redstoner-35/DFEx-FloodBeaMon3tr/PCB/4S六层GaN驱动/生产资料/驱动正面高清图片.JPG

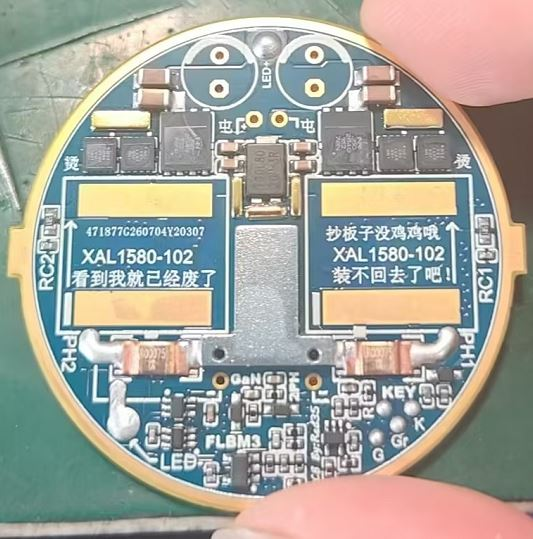
PCB/4S六层GaN驱动/生产资料/驱动正面高清图片.JPG
