redstoner-35/DFEx-FloodBeaMon3tr/PCB/4串主动均衡和BMS/生产资料/变压器样品照片.JPG

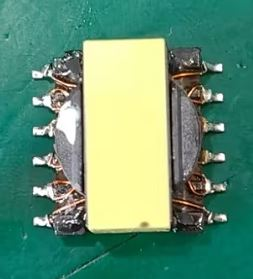
PCB/4串主动均衡和BMS/生产资料/变压器样品照片.JPG
