redstoner-35/DFEx-FloodBeaMon3tr/机械/光学相关文件/光杯尺寸图.jpg

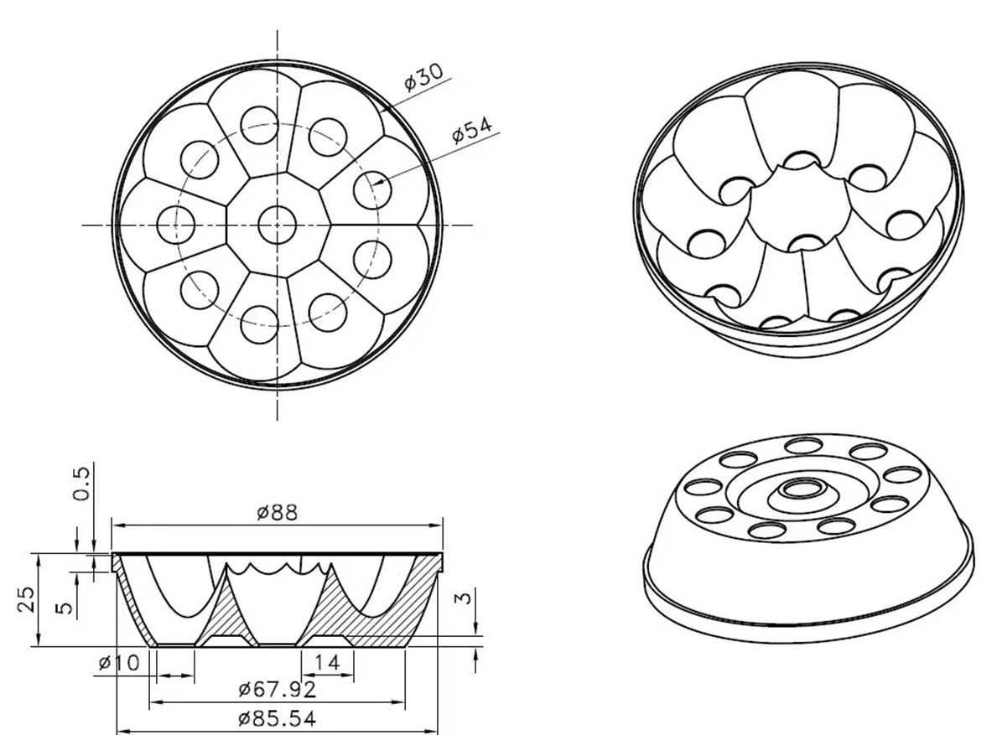
机械/光学相关文件/光杯尺寸图.jpg
