redstoner-35/DFEx-FloodBeaMon3tr/机械/光学相关文件/定位片样式.jpg

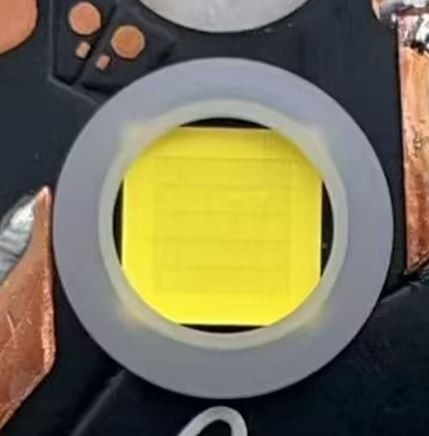
机械/光学相关文件/定位片样式.jpg
