redstoner-35/DFEx-FloodBeaMon3tr/机械/风扇把手相关3D制造文件/风扇手柄固定块.SLDPRT

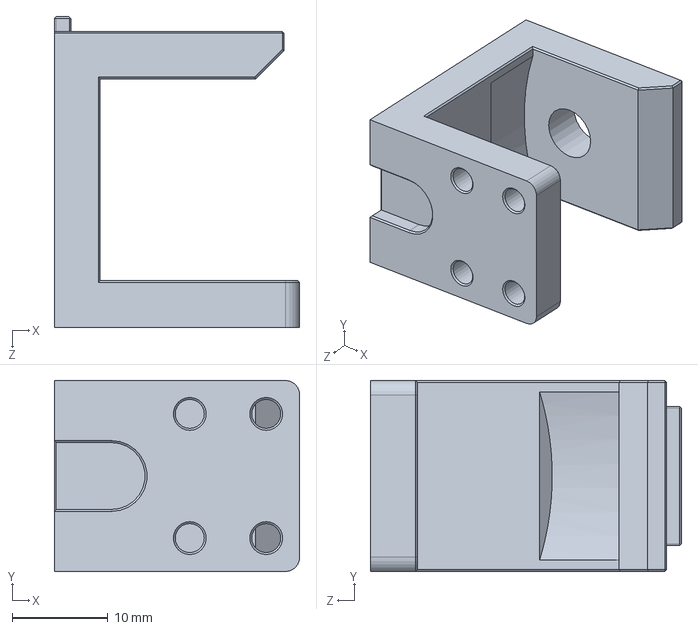
[picture p44: CAD file, 2026-08-25]
机械/风扇把手相关3D制造文件/风扇手柄固定块.SLDPRT
25.7 x 20.0 x 32.5 mm
