redstoner-35/DFEx-FloodBeaMon3tr/机械/驱动相关3D制造文件/驱动电流传导块-紫铜镀雾锡.STEP

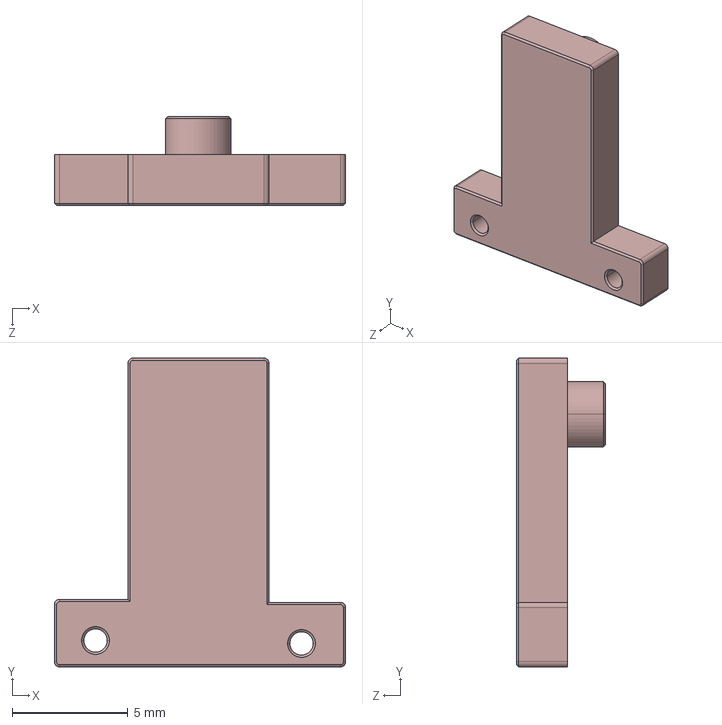
[picture p45: CAD file, 2026-08-21]
机械/驱动相关3D制造文件/驱动电流传导块-紫铜镀雾锡.STEP
12.6 x 13.3 x 3.85 mm
