redstoner-35/DFEx-FloodBeaMon3tr/机械/电池架3D制造文件/3D图/顶部导热块.STEP

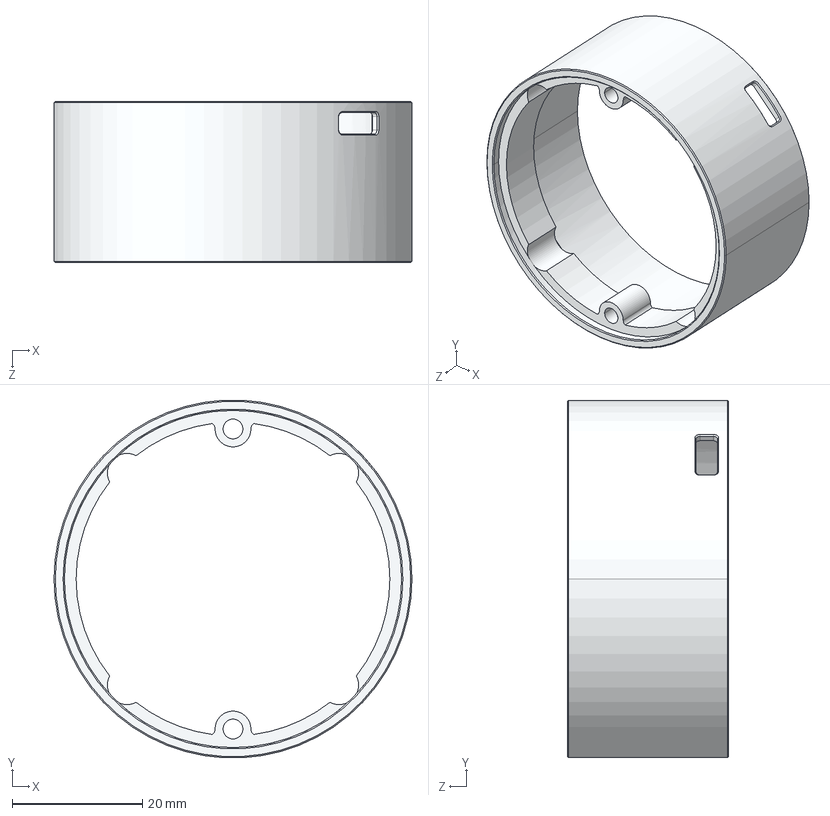
[picture p46: CAD file, 2026-08-21]
机械/电池架3D制造文件/3D图/顶部导热块.STEP
55.0 x 54.9 x 24.8 mm
