redstoner-35/DFEx-FloodBeaMon3tr/机械/电池架3D制造文件/Parts/充电板PCB.SLDPRT

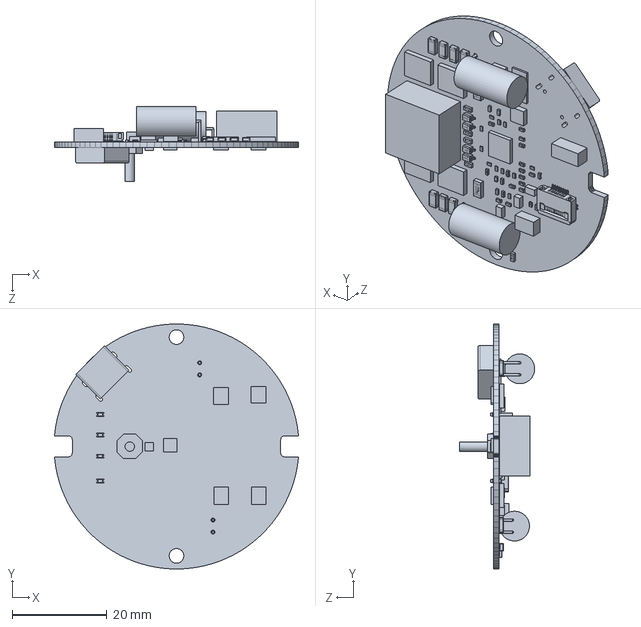
[picture p47: CAD file, 2026-10-09]
机械/电池架3D制造文件/Parts/充电板PCB.SLDPRT
51.4 x 51.6 x 15.9 mm
