redstoner-35/DFEx-FloodBeaMon3tr/机械/筒身3D制造文件/STEP/电池仓.stp

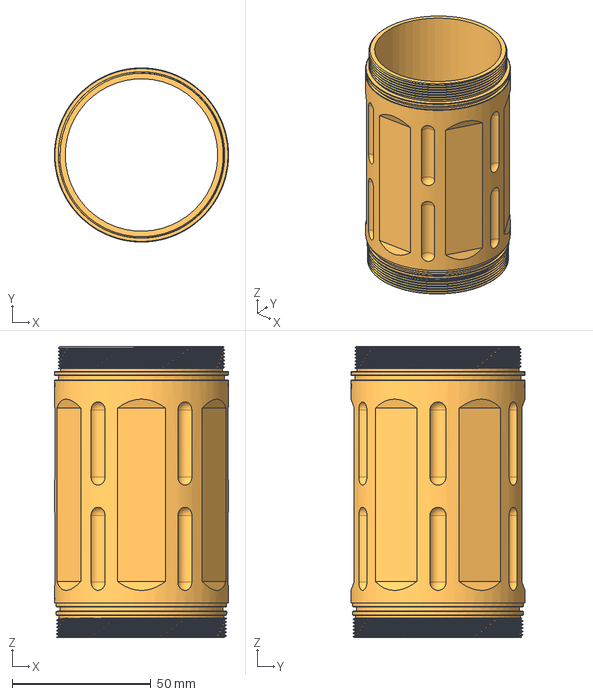
[picture p48: CAD file, 2026-08-21]
机械/筒身3D制造文件/STEP/电池仓.stp
62.9 x 62.9 x 105.0 mm
