redstoner-35/DFEx-FloodBeaMon3tr/机械/风扇把手相关3D制造文件/3D制造文件/40风扇不锈钢夹片-改版.STEP

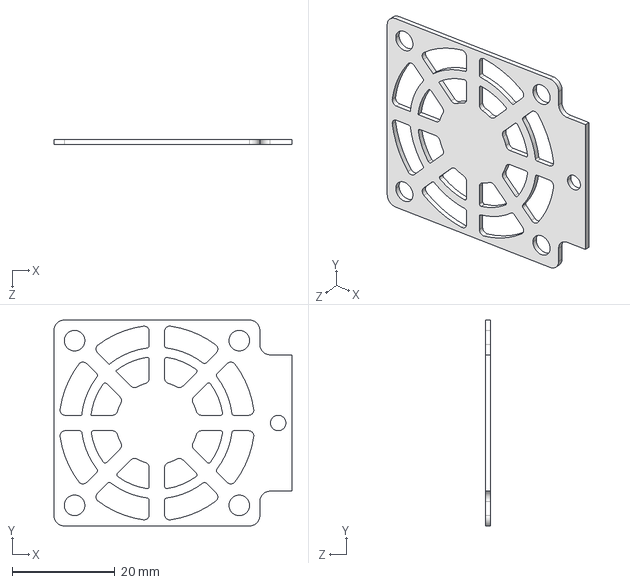
[picture p49: CAD file, 2026-08-21]
机械/风扇把手相关3D制造文件/3D制造文件/40风扇不锈钢夹片-改版.STEP
46.2 x 40.0 x 1.00 mm
