redstoner-35/DFEx-FloodBeaMon3tr/机械/电池架3D制造文件/3D图/电池架底座.STEP

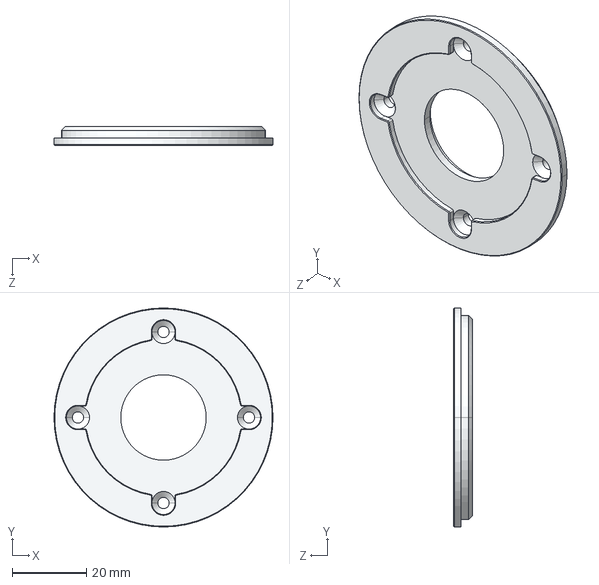
[picture p50: CAD file, 2026-08-21]
机械/电池架3D制造文件/3D图/电池架底座.STEP
59.0 x 59.0 x 5.00 mm
