redstoner-35/DFEx-FloodBeaMon3tr/机械/电池架3D制造文件/Parts/中心铜柱不锈钢螺丝.SLDPRT

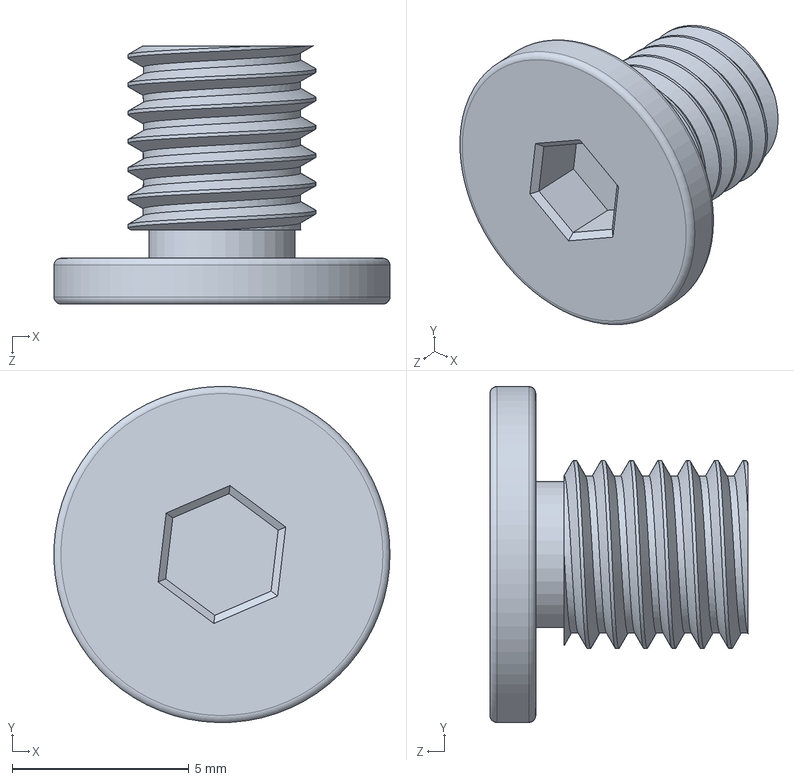
[picture p51: CAD file, 2026-10-09]
机械/电池架3D制造文件/Parts/中心铜柱不锈钢螺丝.SLDPRT
9.50 x 9.50 x 7.30 mm
