redstoner-35/DFEx-FloodBeaMon3tr/机械/筒身3D制造文件/STEP/筒头.stp

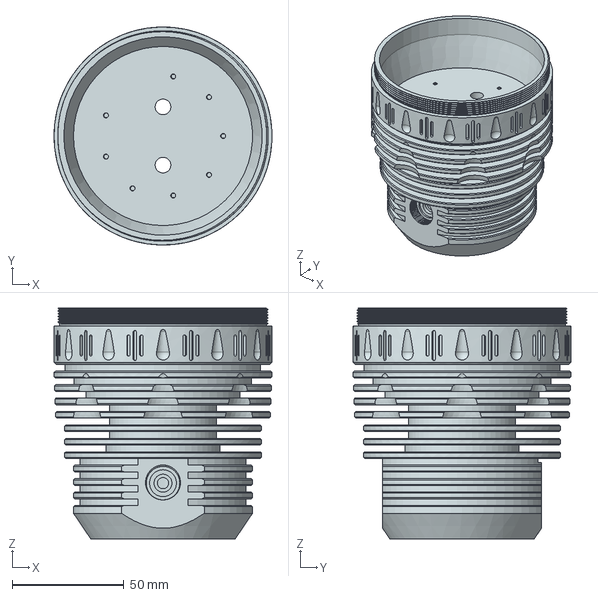
[picture p52: CAD file, 2026-08-21]
机械/筒身3D制造文件/STEP/筒头.stp
97.4 x 97.4 x 103.1 mm
