redstoner-35/DFEx-FloodBeaMon3tr/机械/电池架3D制造文件/Parts/充电板顶部散热铜柱.SLDPRT

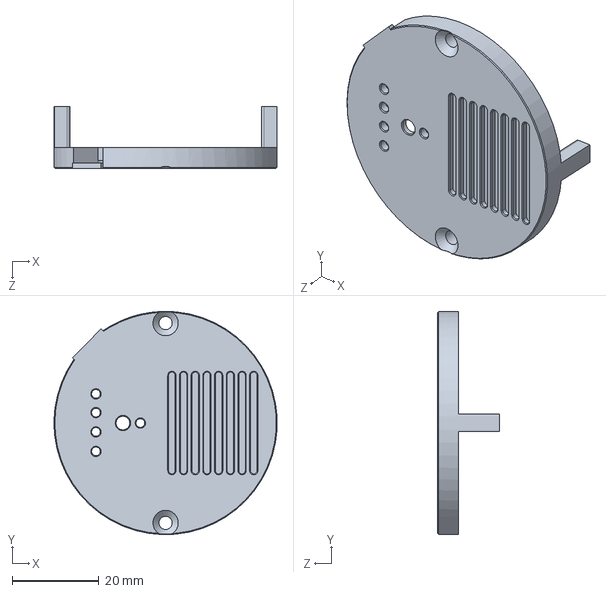
[picture p53: CAD file, 2026-10-09]
机械/电池架3D制造文件/Parts/充电板顶部散热铜柱.SLDPRT
51.5 x 51.5 x 14.2 mm
