redstoner-35/DFEx-FloodBeaMon3tr/机械/电池架3D制造文件/Parts/电池架保护垫圈.SLDPRT

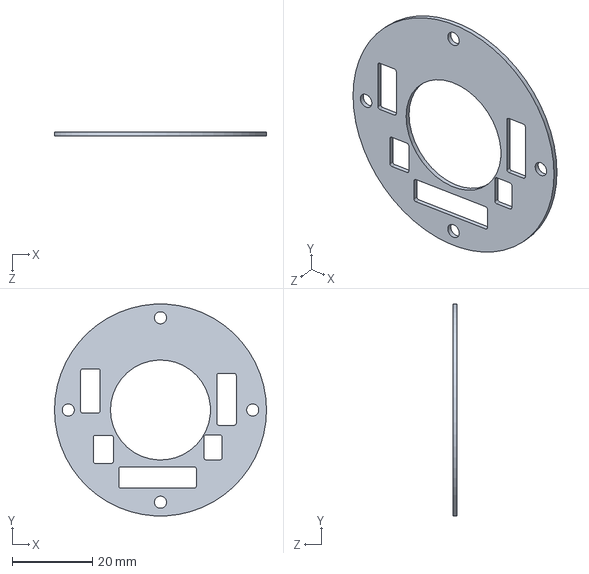
[picture p54: CAD file, 2026-10-09]
机械/电池架3D制造文件/Parts/电池架保护垫圈.SLDPRT
53.0 x 52.9 x 1.00 mm
