redstoner-35/DFEx-FloodBeaMon3tr/机械/电池架3D制造文件/Parts/上端电池接触点.SLDPRT

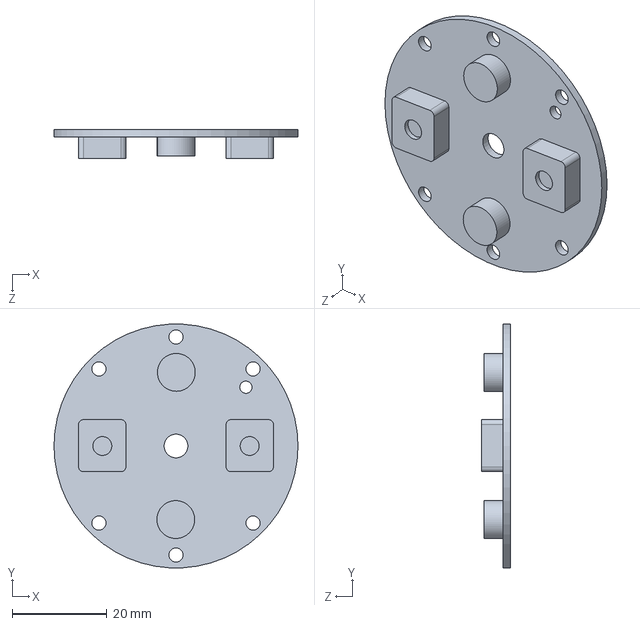
[picture p55: CAD file, 2026-09-21]
机械/电池架3D制造文件/Parts/上端电池接触点.SLDPRT
51.6 x 51.5 x 6.10 mm
