redstoner-35/DFEx-FloodBeaMon3tr/机械/电池架3D制造文件/Parts/正极中通达铜镀金.SLDPRT

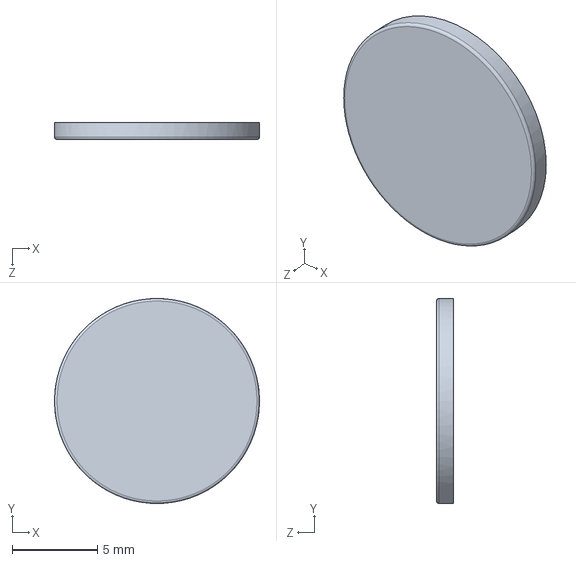
[picture p56: CAD file, 2026-09-21]
机械/电池架3D制造文件/Parts/正极中通达铜镀金.SLDPRT
12.0 x 12.0 x 1.00 mm
