redstoner-35/DFEx-FloodBeaMon3tr/机械/电池架3D制造文件/Parts/下端电池接触板.SLDPRT

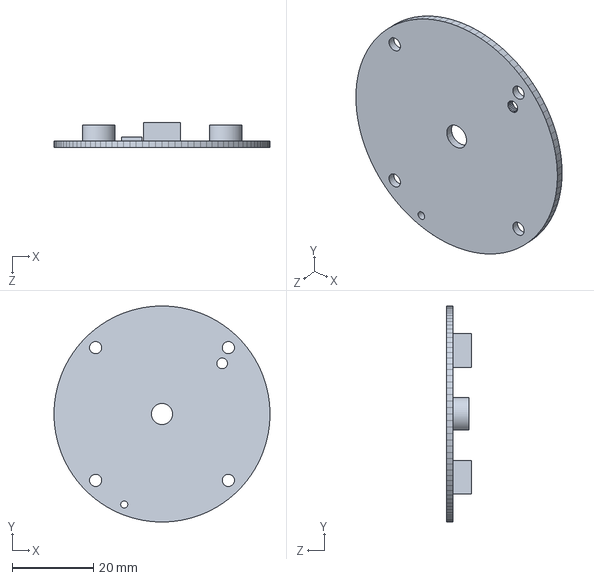
[picture p57: CAD file, 2026-09-21]
机械/电池架3D制造文件/Parts/下端电池接触板.SLDPRT
53.0 x 53.0 x 6.20 mm
