redstoner-35/DFEx-FloodBeaMon3tr/机械/电池架3D制造文件/Parts/正极铜接触点.SLDPRT

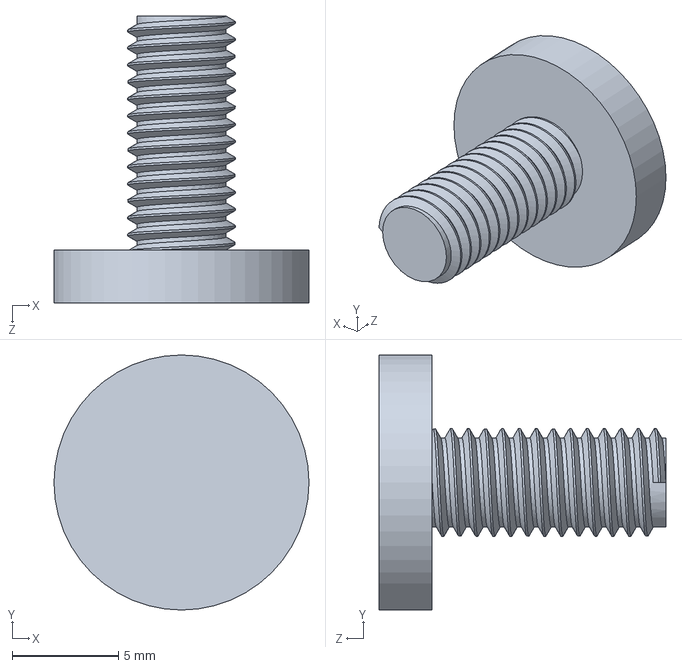
[picture p58: CAD file, 2026-09-21]
机械/电池架3D制造文件/Parts/正极铜接触点.SLDPRT
12.0 x 12.0 x 13.5 mm
