redstoner-35/DFEx-FloodBeaMon3tr/机械/电池架3D制造文件/Parts/同口保护板.SLDPRT

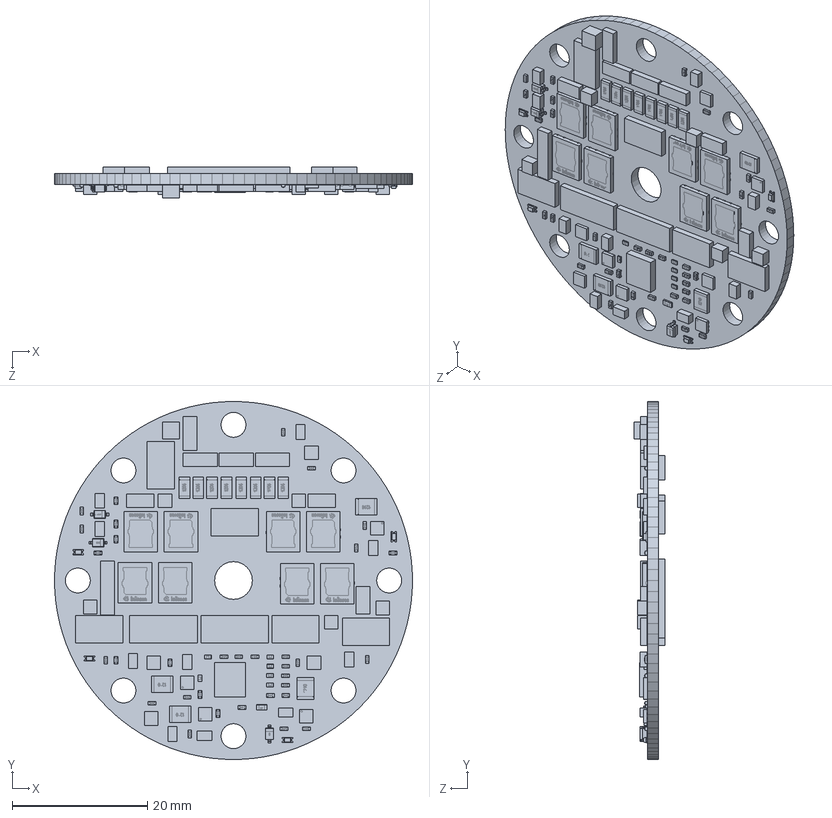
[picture p59: CAD file, 2026-09-21]
机械/电池架3D制造文件/Parts/同口保护板.SLDPRT
53.0 x 53.0 x 4.60 mm
