redstoner-35/DFEx-FloodBeaMon3tr/机械/电池架3D制造文件/Parts/均衡控制板.SLDPRT

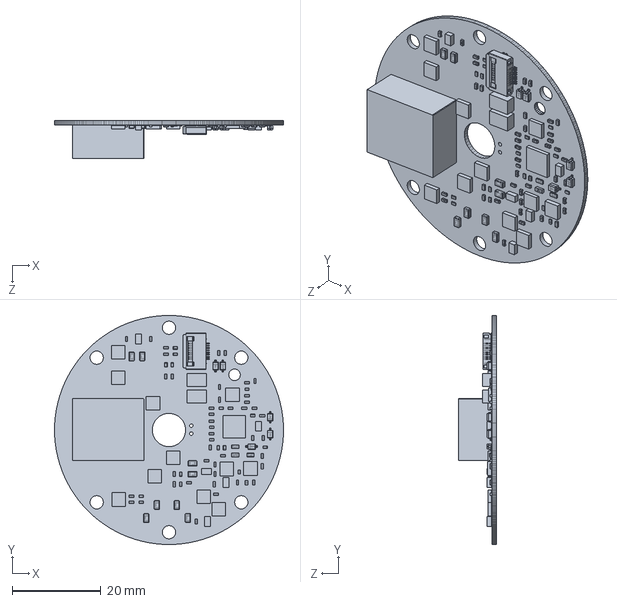
[picture p60: CAD file, 2026-09-21]
机械/电池架3D制造文件/Parts/均衡控制板.SLDPRT
51.6 x 51.6 x 8.50 mm
