redstoner-35/DFEx-FloodBeaMon3tr/机械/电池架3D制造文件/Parts/导电铜柱.SLDPRT

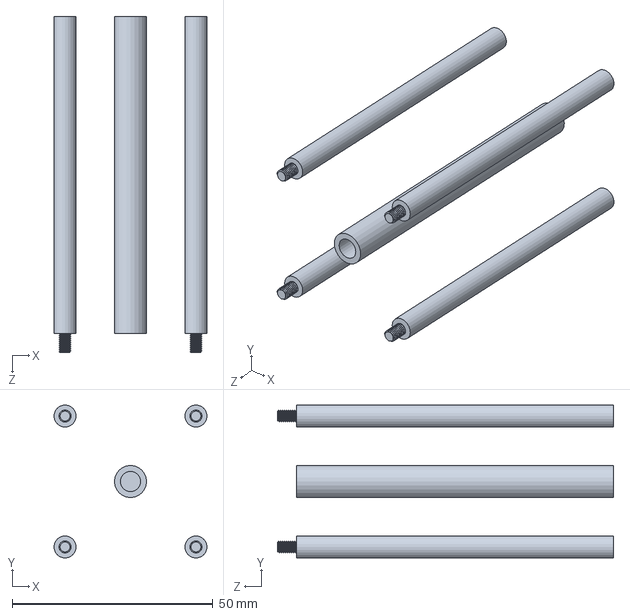
[picture p61: CAD file, 2026-09-21]
机械/电池架3D制造文件/Parts/导电铜柱.SLDPRT
38.1 x 38.1 x 83.7 mm
