redstoner-35/DFEx-FloodBeaMon3tr/固件/驱动固件源码/Logic/ModeControl.c

/****************************************************************************/
/** \file ModeControl.c
/** \Author redstoner_35
/** \Project Xtern Ripper Hyper Boost HV 4S-GaN Edition
/** \Description 这个文件为顶层应用层逻辑文件。负责实现系统所有的挡位切换的换挡
功能，并且实现系统中无极调光功能的具体逻辑模块。

**	History: 

				2026年9月25日  14:11
														 1.新增负责实现挡位记忆更新的函数，解决系统在开机状
															 态下直接进入极亮后，挡位记忆未正确记录进入极亮之
															 前的挡位的问题。
														 
				2025年12月28日 12:42 1.修复QuerySystemFullScaleCurrent()函数中，负责在
															 极亮挡位激活并开启POWER模式时，错误的取出ECO模式
															 的输出电流导致极亮的LM值和电流工作异常。
														 2.针对新的逐步降低恒温控制的逻辑，修改极亮的截断电
															 压改为使用TurboICCMax.h内的宏定义进行统一设置。
														 3.对截止电压进行调整，提高普通挡位的关断阈值。

				2025年12月26日 10:05 1.新增用于走夜路日常照明且具备瞬时爆发输出用来压制
														 远光狗的走夜路挡位，并在挡位参数结构体内注册相关的
														 挡位。
														 2.针对系统多出的新挡位，调整挡位个数至15个。
														 3.新增切换四击常用档功能的配置位QuadClickSel
														 4.针对新挡位在系统关机状态挡位执行的事件处理模块的
															 四击/六击entry处添加对应入口。
														 5.将输出通道状态机负责进行输出电流设定的模块从原来
														   的函数处拆分，改为独立的handler
														 6.配合温控系统的改动根据挡位特性在输出电流合成的处
														   理handler内新增使能\暂停温控计算的对应操作。
														 
				2025年12月20日 Initial Release
**	
*****************************************************************************/
/****************************************************************************/
/*	include files
*****************************************************************************/
#include "SpecialMode.h"
#include "LEDMgmt.h"
#include "SideKey.h"
#include "LocateLED.h"
#include "BattDisplay.h"
#include "OutputChannel.h"
#include "SysConfig.h"
#include "ADCCfg.h"
#include "TempControl.h"
#include "FastOp.h"
#include "LowVoltProt.h"
#include "SelfTest.h"
#include "SOS.h"
#include "Beacon.h"
#include "Strobe.h"
#include "TurboICCMAX.h"
#include "SetupMenu.h"

/****************************************************************************/
/*	Local pre-processor symbols/macros - for Parameter Definition
****************************************************************************/
#define RampAdjustDividingFactor 3 	//无极调光模式下控制调光速度的分频比例，越大则调光速度越慢
#define HoldSwitchDelay 6 					//长按换挡延迟	
#define DischargeThres 3500         //电池放电挡位的结束阈值，单位mV(3500=3.5V)
#define ModeTotalDepth 16 					//系统一共有几个挡位(不能随便调，会炸！)

/****************************************************************************/
/*	Local pre-processor symbols/macros - for Gear System Abstract Layer
****************************************************************************/
#define PauseSwitchGearFlag (HoldChangeGearTIM&0x40) //暂停换挡配置的Flag
#define PosSwitchGearFlag (HoldChangeGearTIM&0x80)  //换挡系统需要顺向往上走一个挡位的Flag
#define InvSwitchGearFlag (HoldChangeGearTIM&0x20)  //换挡系统需要逆序往下走一个挡位的Flag

#define PauseHoldSwitchGear() HoldChangeGearTIM|=0x40 //给换挡系统上Flag，直到用户松开按钮后长按换挡系统才会恢复
#define ClearPosSwitchGearFlag()	HoldChangeGearTIM&=0x7F
#define ClearInvSwitchGearFlag()	HoldChangeGearTIM&=0xDF  //清除逆序和顺序换挡的Flag

/****************************************************************************/
/*	Local pre-processor symbols/macros - for Parameter Display
****************************************************************************/
#message " ****************************************************************************"
#message " *          LED Electrical Parameter & Special Mode Configuration           *"
#message " ****************************************************************************"


//测试模式开启显示低电流
#ifdef EnableTestMode
  #message " Strobe Mode : Limited to 18Amps due to Test Mode Enabled!"
//显示爆闪功率是否小于极亮所以被限制
#elif defined(StrobeIsLessThanTurbo)
  #message " Strobe Mode : Limited to Turbo mode Current due to Turbo Less Than 22Amps"
#elif (StrobeICCMAX < TurboICCMAX)
  #ifdef StrobeLimitedByVTLED
		#message " Strobe Mode : Limited due to protect bonding wire on VT LED."
	#else
	  #message " Strobe Mode : Limited to 22 Amps"
	#endif
#else
  #message " Strobe Mode : Full Power"
#endif

//测试模式开启限流指示
#ifdef EnableTestMode
	#message " Pulse Mode : Limited to 18Amps due to Test Mode Enabled!"
//显示信标功率是否小于极亮所以被限制
#elif defined(BeaconIsLessThanTurbo)
  #message " Pulse Mode : Limited to Turbo mode Current due to Turbo Less Than 22Amps"
#elif (BeaconICCMAX < TurboICCMAX)
  #ifdef StrobeLimitedByVTLED
		#message " Pulse Mode : Limited due to protect bonding wire on VT LED."
	#else
	  #message " Pulse Mode : Limited to 22 Amps"
	#endif
#else
  #message " Pulse Mode : Full Power"
#endif
//测试模式开启,显示开启测试功能
#ifdef EnableTestMode
	#message "LED Type : Unknown LED"
	#message "LED Current : 18A (15A at ECO Mode)"
  #warning "Test Mode Has been Enabled! This FW is only for prototype Testing!"	
//根据LED类型打印极亮电流参数
#elif defined(Custom_LED_ICCMAX)
  #message "LED Type : N/A (defined by project Configuration)"
	#message "LED Current : N/A (defined by project Configuration)"

#elif defined(USING_LED_FV7212D)
	#message "LED Type : DFEx-Super LED+ FV7212D"
  #message "LED Current : 30.3A"
	
#elif defined(USING_LED_FL7022D)|defined(USING_LED_N7175HE)	
	#message "LED Type : DFEx-Super LED+ FL7022D/NightWatch N7-175HE"
  #message "LED Current : 33.0A"
	
#elif defined(USING_LED_FL7018I)
	#message "LED Type : DFEx-Super LED+ FL7018I"
  #message "LED Current : 35.0A"

#elif defined(USING_LED_SFT90X)
	#message "LED Type : Luminus SFT-90-X with 6500K CCT"
  #message "LED Current : 20.0A"
	
#elif defined(USING_LED_NBT160)
	#message "LED Type : NBT160 with 7070 Package"
  #message "LED Current : 28.0A"	

#elif defined(USING_LED_FV7011I)
	#message "LED Type : DFEx-Super LED+ FV7011I"
	#message "LED Current : 35.5A"	
	
#elif defined(USING_LED_N7270HP)
	#message "LED Type : NightWatch N7-270HP"
	#message "LED Current : 35.8A"
	
#elif defined(USING_LED_FL8032P)	
	#message "LED Type : DFEx-Super LED+ FL8032P Gen1"
	#message "LED Current : 41.5A"

#elif defined(USING_LED_FL8032P_G2)	
	#message "LED Type : DFEx-Super LED+ FL8032P Gen2"
	#message "LED Current : 43.75A"
	#message "Note : ECO Current will be increased to 25A for just over 100K Lumens."

#else
	#message "LED Type : Unknown LED"
	#message "LED Current : Undefined"	 

#endif

//如果爆闪电流被限制，则额外弹出提示
#if (StrobeICCMAX == 43200 && TurboICCMAX > 43200)
	#message "Note:Strobe Current is limited to 43.2A to prevent too much stress on driver."
#endif

#message "****************************************************************************"
/****************************************************************************/
/*	Local constant variable definitions('static const 'or 'code')
****************************************************************************/

//挡位结构体
code ModeStrDef ModeSettings[ModeTotalDepth]=
	{
		//关机状态
    {
		Mode_OFF,
		0,
		0,  //电流0mA
		0,  //关机状态阈值为0强制解除警报
		true,
		false,
		//配置是否允许进入爆闪
		true,
		//低电量保护设置
		Mode_OFF,							 //低电量触发保护之后，如果不执行关机则自动跳转的挡位
		LVPROT_Disable,        //低电量保护机制的类型
		//挡位切换设置
		Mode_OFF,
		Mode_OFF	 //模式挡位切换设置，长按和单击+长按切换到的目标挡位(输入OFF表示不进行切换)
		}, 
		//出错了
		{
		Mode_Fault,
		0,
		0,  //电流0mA
		0,
		false,
		false,
		//配置是否允许进入爆闪
		false,
		//低电量保护设置
		Mode_OFF,							 //低电量触发保护之后，如果不执行关机则自动跳转的挡位
		LVPROT_Disable,        //低电量保护机制的类型
		//挡位切换设置
		Mode_OFF,
		Mode_OFF	 //模式挡位切换设置，长按和单击+长按切换到的目标挡位(输入OFF表示不进行切换)
		}, 
		//月光
		{
		Mode_Moon,
		CalcIREFValue(35),         //35mA
		0,   //最小电流没用到，无视
		2750,  //2.75V关断
		false, //月光档有专用入口，无需带记忆
		false,
		//配置是否允许进入爆闪
		false,
		//低电量保护设置
		Mode_Moon,							 //低电量触发保护之后，如果不执行关机则自动跳转的挡位
		LVPROT_Enable_OFF,        //低电量保护机制的类型
		//挡位切换设置
		Mode_OFF,
		Mode_1Lumen,	 //模式挡位切换设置，长按和单击+长按切换到的目标挡位(输入OFF表示不进行切换)
		}, 	
		//1流明挡位
		{
		Mode_1Lumen,
		2,  //电流随便填的
		0,   //最小电流没用到，无视
		2500,  //2.5V关断（1流明没有保护）
		false, //1流明档有专用入口，无需带记忆
		false,	
		//配置是否允许进入爆闪
		false,
		//低电量保护设置
		Mode_1Lumen,							 //低电量触发保护之后，如果不执行关机则自动跳转的挡位
		LVPROT_Disable,        		 //低电量保护机制的类型
		//挡位切换设置
		Mode_Moon,
		Mode_OFF	 //模式挡位切换设置，长按和单击+长按切换到的目标挡位(输入OFF表示不进行切换)			
		},
		//极低亮
		{
		Mode_ExtremelyLow,
		CalcIREFValue(200),  //200mA
		0,   //最小电流没用到，无视
		2900,  //2.9V关断
		true, //带记忆
		false,
		//配置是否允许进入爆闪
		true,
		//低电量保护设置
		Mode_ExtremelyLow,							 //低电量触发保护之后，如果不执行关机则自动跳转的挡位
		LVPROT_Enable_OFF,        //低电量保护机制的类型
		//挡位切换设置
		Mode_Low,
		Mode_OFF	 //模式挡位切换设置，长按和单击+长按切换到的目标挡位(输入OFF表示不进行切换)
		}, 	
    //低亮
		{
		Mode_Low,
		CalcIREFValue(650),  //650mA电流
		0,   //最小电流没用到，无视
		2950,  //2.95V关断
		true,
		false,
		//配置是否允许进入爆闪
		true,
		//低电量保护设置
		Mode_ExtremelyLow,				 //低电量触发保护之后，如果不执行关机则自动跳转的挡位
		LVPROT_Enable_Jump,        //低电量保护机制的类型
		//挡位切换设置
		Mode_Mid,
		Mode_ExtremelyLow	 //模式挡位切换设置，长按和单击+长按切换到的目标挡位(输入OFF表示不进行切换)
		},
    //中亮
		{
		Mode_Mid,
		CalcIREFValue(1600),  //1600mA电流
		0,   //最小电流没用到，无视
		3050,  //3.05V关断
		true,
		false,
		//配置是否允许进入爆闪
		true,
		//低电量保护设置
		Mode_Low,				 //低电量触发保护之后，如果不执行关机则自动跳转的挡位
		LVPROT_Enable_Jump,        //低电量保护机制的类型
		//挡位切换设置
		Mode_MHigh,
		Mode_Low	 //模式挡位切换设置，长按和单击+长按切换到的目标挡位(输入OFF表示不进行切换)
		}, 	
    //中高亮
		{
		Mode_MHigh,
		CalcIREFValue(3250),  //3250mA电流
		0,   //最小电流没用到，无视
		3150,  //3.15V关断
		true,
		true,
		//配置是否允许进入爆闪
		true,
		//低电量保护设置
		Mode_Mid,				 //低电量触发保护之后，如果不执行关机则自动跳转的挡位
		LVPROT_Enable_Jump,        //低电量保护机制的类型
		//挡位切换设置
		Mode_High,
		Mode_Mid	 //模式挡位切换设置，长按和单击+长按切换到的目标挡位(输入OFF表示不进行切换)
		}, 	
    //高亮
		{
		Mode_High,
		CalcIREFValue(7000),  //7000mA电流
		0,   //最小电流没用到，无视
		3250,  //3.25V关断
		true,
		true,
		//配置是否允许进入爆闪
		true,
		//低电量保护设置
		Mode_MHigh,				 //低电量触发保护之后，如果不执行关机则自动跳转的挡位
		LVPROT_Enable_Jump,        //低电量保护机制的类型
		//挡位切换设置
		Mode_ExtremelyLow,
		Mode_MHigh	 //模式挡位切换设置，长按和单击+长按切换到的目标挡位(输入OFF表示不进行切换)
		}, 	
    //极亮
		{
		Mode_Turbo,
		CalcIREFValue(TurboICCMAX),  //30A电流	
		0,   //最小电流没用到，无视
		TurboOFFVoltage,  //使用配置文件的关断值
		false, //极亮不能带记忆
		true,
		//配置是否允许进入爆闪
		false,
		//低电量保护设置
		Mode_Turbo,				 //低电量触发保护之后，如果不执行关机则自动跳转的挡位
		LVPROT_Disable,        //低电量保护机制的类型
		//挡位切换设置
		Mode_OFF,
		Mode_High	 //模式挡位切换设置，长按和单击+长按切换到的目标挡位(输入OFF表示不进行切换)
		}, 	
    //爆闪		
		{
		Mode_Strobe,
		CalcIREFValue(StrobeICCMAX),		
		0,   //最小电流没用到，无视
		2750,  //2.75V关断
		false, //爆闪不能带记忆
		true,
		//配置是否允许进入爆闪
		false,
		//低电量保护设置
		Mode_Strobe,				 //低电量触发保护之后，如果不执行关机则自动跳转的挡位
		LVPROT_Enable_OFF,        //低电量保护机制的类型
		//挡位切换设置
		Mode_SOS,
		Mode_Beacon	 //模式挡位切换设置，长按和单击+长按切换到的目标挡位(输入OFF表示不进行切换)
		}, 
	  //无极调光		
		{
		Mode_Ramp,
		CalcIREFValue(10000),  //最大 10000mA电流
		CalcIREFValue(150),   //最小 150mA电流
		3200,  //3.2V关断
		false, //不能带记忆  
		true,
		//配置是否允许进入爆闪
		true,
		//低电量保护设置
		Mode_Ramp,				 //低电量触发保护之后，如果不执行关机则自动跳转的挡位
		LVPROT_Disable,        //低电量保护机制的类型
		//挡位切换设置
		Mode_OFF,
		Mode_OFF	 //模式挡位切换设置，长按和单击+长按切换到的目标挡位(输入OFF表示不进行切换)
		}, 
		//信标模式
		{
		Mode_Beacon,
		CalcIREFValue(BeaconICCMAX),
		0,   //最小电流没用到，无视
		2750,  //2.75V关断
		false,	//信标不能带记忆
		true,
		//配置是否允许进入爆闪
		false,
		//低电量保护设置
		Mode_Beacon,				 //低电量触发保护之后，如果不执行关机则自动跳转的挡位
		LVPROT_Enable_OFF,        //低电量保护机制的类型
		//挡位切换设置
		Mode_Strobe,
		Mode_SOS	 //模式挡位切换设置，长按和单击+长按切换到的目标挡位(输入OFF表示不进行切换)
		}, 
	  //SOS
		{
		Mode_SOS,
		CalcIREFValue(10500),  //10.5A电流
		0,   //最小电流没用到，无视
		2750,  //2.75V关断
		false,	//SOS不能带记忆
		true,
		//配置是否允许进入爆闪
		false,
		//低电量保护设置
		Mode_SOS,				 //低电量触发保护之后，如果不执行关机则自动跳转的挡位
		LVPROT_Enable_OFF,        //低电量保护机制的类型
		//挡位切换设置
		Mode_Beacon,
		Mode_Strobe	 //模式挡位切换设置，长按和单击+长按切换到的目标挡位(输入OFF表示不进行切换)
		}, 
		//制裁远光狗模式
		{
		Mode_FuckDog,
		CalcIREFValue(StrobeICCMAX),  //按下全功率爆闪
		CalcIREFValue(1100),   //默认松手的电流（1.1A）
		2900,  //2.90V关断
		false,	//不能带记忆
		true,
		//配置是否允许进入爆闪
		false,
		//低电量保护设置
		Mode_FuckDog,				 //低电量触发保护之后，如果不执行关机则自动跳转的挡位
		LVPROT_Enable_OFF,        //低电量保护机制的类型
		//挡位切换设置
		Mode_OFF,
		Mode_OFF	 //模式挡位切换设置，长按和单击+长按切换到的目标挡位(输入OFF表示不进行切换)
		},	
		//电池放电模式
		{
		Mode_Discharge,
		CalcIREFValue(3500),  //最大3500mA
		CalcIREFValue(300),   									//最小电流设定在接近放电尾声的电流
		DischargeThres,  			//指定阈值关断
		false,	//不能带记忆
		true,
		//配置是否允许进入爆闪
		false,
		//低电量保护设置
		Mode_Discharge,				 //低电量触发保护之后，如果不执行关机则自动跳转的挡位
		LVPROT_Enable_OFF,        //低电量保护机制的类型
		//挡位切换设置
		Mode_OFF,
		Mode_OFF	 //模式挡位切换设置，长按和单击+长按切换到的目标挡位(输入OFF表示不进行切换)
		},			
	};

/****************************************************************************/
/*	Global variable definitions - System Gear Switching Related
****************************************************************************/	
ModeStrDef *CurrentMode; 					//当前挡位数据（指针，指向挡位结构体）
xdata ModeIdxDef LastMode; 				//挡位记忆存储
xdata ModeIdxDef LastSpecialMode; //特殊功能挡位存储
SysConfigDef SysCfg; 							//系统配置	
bit IsStrobePoweredFromOFF; 			//是否为关机模式下进入到一键爆闪
	
/****************************************************************************/
/*	Global Flag definitions - System Configuration
****************************************************************************/		
bit IsRampEnabled; //是否开启无极调光
bit IsMainMemEnabled; //是否开启主挡位记忆
bit IsSpecMemEnabled; //是否开启特殊挡位记忆
bit IsPowerModeEnabled; //0=ECO MODE 1=POWER MODE		
bit QuadClickSel;     //四击动作选择，0=战术模式，1=走夜路+远光狗制裁模式	
	
/****************************************************************************/
/*	Global variable definitions - Special Timers
****************************************************************************/		
xdata unsigned char DisplayLockedTIM; //锁定和战术模式进入退出显示	
	
/****************************************************************************/
/*	Local variable definitions('static') for Ramp Systems
****************************************************************************/		
static xdata unsigned char RampDIVCNT; //无极调光降低调光速度的分频计时器		
static bit IsRampKeyPressed;  //标志位，用户是否按下按键对无极调光进行调节
static bit IsNotifyMaxRampLimitReached; //标记无极调光达到最大电流	

/****************************************************************************/
/*	Local variable definitions('static') for Other Usage
****************************************************************************/		
static xdata unsigned char HoldChangeGearTIM; //挡位模式下长按换挡
static bit IsSlowFading; 											//关机渐暗特效
static bit IsBatteryNearDrained;  						//电池是否已经接近放空
static bit IsSwitchingKeyStillHold; 					//按键是否仍然按住

/********************************************************************************/
/* local Function implementation - Mode Memory Related
*********************************************************************************/

//特殊功能挡位独立记忆的处理函数
static void SpecialModeMemoryHandler(void)	
	{
	//关闭特殊挡位记忆
	if(!IsSpecMemEnabled)return;
	//关机状态下三击爆闪，不进行记忆，立即清除flag
	if(IsStrobePoweredFromOFF)IsStrobePoweredFromOFF=0;
	//非关机状态下一键爆闪和战术模式，存储下离开或者关机之前的特殊功能挡位
	else if(!SysMode)LastSpecialMode=CurrentMode->ModeIdx;
	}
	
/********************************************************************************/
/* local Function implementation - Table Driver based Gear Switching System 
	 related stuff
*********************************************************************************/	

//进行关机和开机状态执行N击+长按事件处理的函数
static void ProcessNClickAndHoldHandler(void)
	{
  //正常执行处理
	switch(getSideKeyNClickAndHoldEvent())
		{
		case 1:	//单击+长按进入1流明挡位(仅系统处于关机后)
			if(CurrentMode->ModeIdx!=Mode_OFF)break;
			SwitchToGear(Mode_1Lumen);
			break; 
		case 2:TriggerVshowDisplay();break; //双击+长按查询电量
		case 3:TriggerTShowDisplay();break;//三击+长按查询温度
		//其余情况什么都不做
		default:break;			
		}
	}		

//进行模式状态机的表驱动模块处理	
static void ModeSwitchFSMTableDriver(char ClickCount)
	{
	if(CurrentMode->IsEnterTurboStrobe)TryEnterTurboStrobeProcess(ClickCount);//读取当前的模式结构体，执行进入极亮或者爆闪的检测	
  if(IsLargerThanOneU8(CurrentMode->ModeIdx)) //大于1的比较									
		{
		//系统在开机状态，且标志位无效之后则执行电量显示启动检测
		ProcessNClickAndHoldHandler();
		//侧按单击或者在战术模式下松开按钮时关机	
		if(!SysMode)
				{
				//非战术模式单击关闭
				if(ClickCount==1)ReturnToOFFState();
				}
		else if(!getSideKeyHoldEvent())ReturnToOFFState();
		}			
	
 	if(PosSwitchGearFlag)	 
		{
		//当挡位数据库内的状态表使能长按换挡功能且条件满足时，执行顺向换挡
		ClearPosSwitchGearFlag();
		if(CurrentMode->ModeTargetWhenH!=Mode_OFF)SwitchToGear(CurrentMode->ModeTargetWhenH); 		
		}
	
	if(InvSwitchGearFlag)  
		{
		//当挡位数据库内的状态表使能单击+长按换挡功能且条件满足时，执行逆向换挡
		ClearInvSwitchGearFlag();
		if(CurrentMode->ModeTargetWhen1H!=Mode_OFF)SwitchToGear(CurrentMode->ModeTargetWhen1H); 
		}
	
	if(CurrentMode->LVConfig)BatteryLowAlertProcess(CurrentMode->LVConfig&0x02,CurrentMode->ModeWhenLVAutoFall); //执行低电量处理
	}	

/********************************************************************************/
/* local Function implementation - Ramp Mode Logic Handler
*********************************************************************************/	
static void RampAdjHandler(void)	
	{	
	//无极调光处理
  int Limit;
	bit IsPress;
  //计算出无极调光上限
	IsPress=getSideKey1HEvent()|getSideKeyHoldEvent();
	Limit=SysCfg.RampCurrentLimit<CurrentMode->Current?SysCfg.RampCurrentLimit:CurrentMode->Current;
	//在电流被限制的情况下用户按下按键尝试调整电流，立即限幅
	if(Limit<CurrentMode->Current&&IsPress&&SysCfg.RampCurrent>Limit)SysCfg.RampCurrent=Limit; 
	//进行亮度调整
	if(getSideKeyHoldEvent()&&!IsRampKeyPressed) //长按增加电流
			{	
			if(RampDIVCNT)RampDIVCNT--;
			else 
				{
				//时间到，开始增加电流
				if(SysCfg.RampCurrent<Limit)SysCfg.RampCurrent++;
				else
					{
					IsNotifyMaxRampLimitReached=1; //标记已达到上限
					SysCfg.RampLimitReachDisplayTIM=4; //熄灭0.5秒指示已经到上限
					SysCfg.RampCurrent=Limit; //限制电流最大值	
					IsRampKeyPressed=1;
					}
				//计时时间到，复位变量
				RampDIVCNT=RampAdjustDividingFactor;
				}
			}	
	else if(getSideKey1HEvent()&&!IsRampKeyPressed) //单击+长按减少电流
		 {
			if(RampDIVCNT)RampDIVCNT--;
			else
				{
				if(SysCfg.RampCurrent>CurrentMode->MinCurrent)SysCfg.RampCurrent--; //减少电流	
				else
					{
					IsNotifyMaxRampLimitReached=0;
					SysCfg.RampLimitReachDisplayTIM=4; //熄灭0.5秒指示已经到下限
					SysCfg.RampCurrent=CurrentMode->MinCurrent; //限制电流最小值
					IsRampKeyPressed=1;
					}
				//计时时间到，复位变量
				RampDIVCNT=RampAdjustDividingFactor;
				}
		 }
  else if(!IsPress&&IsRampKeyPressed)
		{
	  IsRampKeyPressed=0; //用户放开按键，允许调节		
		RampDIVCNT=RampAdjustDividingFactor; //复位分频计时器
		}
	//进行数据保存的判断
	if(IsPress)SysCfg.CfgSavedTIM=32; //按键按下说明正在调整，复位计时器
	else if(SysCfg.CfgSavedTIM==1)
		{
		SysCfg.CfgSavedTIM--;
		if(IsMainMemEnabled)SaveSysConfig(0);  //一段时间内没操作说明已经调节完毕，保存数据
		}
	}	
	
/********************************************************************************/
/* Global Function implementation - Initialization
*********************************************************************************/		

//初始化模式状态机
void ModeFSMInit(void)
	{
	bool Result;
  //复位故障码和挡位模式配置系统
	ResetStrobeModule(); 											//复位爆闪控制器
	LastMode=Mode_ExtremelyLow;
	LastSpecialMode=Mode_Strobe;
	ErrCode=Fault_None; 					//没有故障
	//初始化无极调光
	SysCfg.RampLimitReachDisplayTIM=0;
  ReadSysConfig(); //从EEPROM内读取无极调光配置
	
	CurrentMode=FindTargetMode(Mode_Ramp,&Result);//遍历挡位设置结构体寻找无极调光的挡位并读取配置
	if(Result)
		{
		SysCfg.RampBattThres=CurrentMode->LowVoltThres; //低压检测上限恢复
		SysCfg.RampCurrentLimit=CurrentMode->Current; //找到挡位数据中无极调光的挡位，电流上限恢复
		if(SysCfg.RampCurrent<CurrentMode->MinCurrent)SysCfg.RampCurrent=CurrentMode->MinCurrent;
		if(SysCfg.RampCurrent>SysCfg.RampCurrentLimit)SysCfg.RampCurrent=SysCfg.RampCurrentLimit;		//读取数据结束后，检查读入的数据是否合法，不合法就直接修正
		CurrentMode=&ModeSettings[0]; 					//记忆重置为第一个档
		}
	//无法找到无极调光数值，挡位数据损毁，报错
  else ReportError(Fault_RampConfigError);
	//复位变量和一部分模块
	DisplayLockedTIM=0;
	IsSlowFading=0;
	SetupFSMState=SetupMenu_InACT;            //复位设置状态机
	RampDIVCNT=RampAdjustDividingFactor; 			//复位分频计数器	
	}	

/********************************************************************************/
/* Global Function implementation - Gear Switching Related
*********************************************************************************/	

//输入指定的Index，从index里面找到目标模式结构体并返回指针
ModeStrDef *FindTargetMode(ModeIdxDef Mode,bool *IsResultOK)
	{
	unsigned char i;
	*IsResultOK=false;
	for(i=0;i<ModeTotalDepth;i++)if(ModeSettings[i].ModeIdx==Mode)
		{
		*IsResultOK=true;
		break;
		}
	//返回对应的index
	return &ModeSettings[i];
	}
	
//挡位跳转
void SwitchToGear(ModeIdxDef TargetMode)
	{
	bool IsLastModeNeedStepDown,Result;
	ModeStrDef *ModeBuf;
	//当前挡位已经是目标值，不执行
	if(TargetMode==CurrentMode->ModeIdx)return;
	//记录换档前的结果	
	IsLastModeNeedStepDown=CurrentMode->IsNeedStepDown; //存下是否需要降档
	//开始寻找
	ModeBuf=FindTargetMode(TargetMode,&Result);
	if(!Result)return;                    //找不到对应的挡位，退出
	//应用挡位结果并重新计算极亮电流	
	CurrentMode=ModeBuf;	
	CalcTurboILIM();
	//复位特殊功能挡位至初始状态
	ResetSOSModule();						//复位整个SOS模块
	BeaconFSM_Reset(); 					//复位整个信标模块	
			
	//如果新老挡位都是常亮挡，则重新设置PI环避免电流过调
	if(TargetMode>1&&TargetMode<11&&IsLastModeNeedStepDown)RecalcPILoop(); 	
	}	

//挡位记忆处理
void ModeMemoryHandler(void)
	{
	//系统关闭挡位记忆，如果当前是无极调光，则恢复到初始电流
	if(!IsMainMemEnabled)
		{
		if(IsRampEnabled)		//无极调光开启，恢复到最低电流
			{
			LoadMinimumRampCurrentToRAM();
			SaveSysConfig(0);                //保存一遍配置，确保写入到EEPROM里面的数据一定是最低电流
			}
		//非无极调光模式，记忆恢复到最低挡位
		else LastMode=Mode_ExtremelyLow;
		}
	//系统开启挡位记忆，进行写入
	else if(CurrentMode->IsModeHasMemory)
		{
		if(CurrentMode->ModeIdx<5||CurrentMode->ModeIdx>9)return; //非循环挡位，不允许记忆
		LastMode=CurrentMode->ModeIdx;
		}
	}	
	
//执行关机处理的函数	
void ReturnToOFFState(void)
	{
	switch(CurrentMode->ModeIdx)
		{
		case Mode_Fault:
		case Mode_OFF:return;  //非法状态，直接打断整个函数的执行
		case Mode_Beacon:
		case Mode_Strobe:	//特殊挡位执行记忆函数，且不启用慢速关闭
		case Mode_SOS:
			  SpecialModeMemoryHandler();
			  break; 

		//其余挡位如果非特殊模式，则执行判断
		default:
			if(SysMode)break;
			if(CurrentMode->IsNeedStepDown)Current=CurrentBuf; //如果当前挡位需要温控，则在关机的时候直接取目前已执行的电流结果
			IsSlowFading=1;	//非战术模式的常亮挡位触发渐暗特效
		}
	//执行挡位记忆和关机处理，强制跳回到关机挡位
	ModeMemoryHandler();
	SwitchToGear(Mode_OFF); 
	}		
	
/********************************************************************************/
/* Global Function implementation - Output or Special Current Fetch
*********************************************************************************/		

//获取系统挡位在没有任何外部影响情况下的全部电流
int QuerySystemFullScaleCurrent(void)
	{
	if(CurrentMode->ModeIdx==Mode_Turbo&&!IsPowerModeEnabled)
		{
		//极亮且开启ECO模式，电流按照ECO模式的ICCMAX取,限制输出功率
		return CalcIREFValue(ECOTurboICCMAX);
		}
	//其他情况按照极亮当前电流取
  return QueryCurrentGearILED();	
	}
	
//特殊挡位电流处理
void SpecialModeCurrentFetch(void)
	{
	switch(BattState)//取出挡位电流
			{
			case Battery_Plenty:
			case Battery_Mid:Current=QueryCurrentGearILED();break;
      case Battery_Low:Current=CalcIREFValue(10000);break;
			case Battery_VeryLow:Current=CalcIREFValue(4000);break;
			}
	//仅允许在电量充足，开启全功率爆闪的时候，开启高频爆闪Halt
	if(QueryIfBatteryIsLow())IsHighPowerStrobe=0;	
	//电流限幅功能（若ECO模式开启，则特殊功能挡位的最大电流强制限制为ECO电流）
	if(!IsPowerModeEnabled&&Current>CalcIREFValue(ECOTurboICCMAX))Current=CalcIREFValue(ECOTurboICCMAX);		
	}	
	
/********************************************************************************/
/* Global Function implementation - Gear Switching Timing Handler
*********************************************************************************/		
	
//挡位状态机所需的软件定时器处理
void ModeFSMTIMHandler(void)
{
	//无极调光相关的定时器
	if(IsLargerThanOneU8(SysCfg.CfgSavedTIM))SysCfg.CfgSavedTIM--;
	if(SysCfg.RampLimitReachDisplayTIM)
		{
		SysCfg.RampLimitReachDisplayTIM--;
		if(!SysCfg.RampLimitReachDisplayTIM)IsNotifyMaxRampLimitReached=0;
		}
	//锁定操作提示计时器
  if(DisplayLockedTIM)DisplayLockedTIM--;
}	
	
//长按换挡的间隔命令生成
void HoldSwitchGearCmdHandler(void)
	{
	char buf;
	if(SysMode||(!getSideKeyHoldEvent()&&!getSideKey1HEvent()))//按键松开或者系统处在非正常状态，计时器和Flag复位
		{
		IsSwitchingKeyStillHold=0;
		HoldChangeGearTIM=0; 
		}
	else //执行换挡程序
		{
		buf=HoldChangeGearTIM&0x1F; //取出TIM值
		if(!buf&&!(HoldChangeGearTIM&0x40))//令换挡命令位1指示换挡可以继续
			{
			IsSwitchingKeyStillHold=1;
			HoldChangeGearTIM|=getSideKey1HEvent()?0x20:0x80; 
			}
		HoldChangeGearTIM&=0xE0; //去除掉原始的TIM值
		if(buf<HoldSwitchDelay&&!PauseSwitchGearFlag)buf++;
		else buf=0;  //时间到，清零结果
		HoldChangeGearTIM|=buf; //把数值写回去
		}
	}	
	
/********************************************************************************/
/* Global Function implementation - Gear Switching Logic(FSM) Handler
*********************************************************************************/		
	
//挡位状态机
void ModeSwitchFSM(void)
	{
	unsigned char ClickCount;
	ModeIdxDef ModeBeforeFSMSwitch;
	//获取按键状态
	if(GetIfSystemInPOFFSeq())return; //系统处于关机过程中，不执行按键处理
	ClickCount=getSideKeyShortPressCount();	//读取按键处理函数传过来的参数
		
	//挡位记忆参数检查
	if(LastSpecialMode<11||LastSpecialMode>13)LastSpecialMode=Mode_Strobe;        //特殊功能
	if(LastMode<2||LastMode>13)LastMode=Mode_ExtremelyLow;									//全局常规记忆
		
	//处理FSM的特殊逻辑部分		
  ModeBeforeFSMSwitch=CurrentMode->ModeIdx;		 //存下进入之前的挡位
	IsHalfBrightness=0; //按键灯默认全亮
	switch(ModeBeforeFSMSwitch)	
		{
		//关机状态
		case Mode_OFF:		  
			//处理特殊功能和定位LED和其他设置的变更(在变更和特殊模式下拒绝执行其他内容)
		  if(SetupFSMState!=SetupMenu_InACT||LocateLED_Edit())break;
			else if(SpecialModeOperation(ClickCount)!=Operation_Normal)break;
		  
		  //非特殊模式正常单击开关机，执行一键极亮，爆闪和转换无极调光
			switch(ClickCount)
				{
				case 1:
					//侧按单击开机，进入循环挡位上一次关闭的模式
					PowerToNormalMode(LastMode);
					break; 	
				case 4:
					//在开启夜行模式的时候四击进入。
				  if(QuadClickSel)SwitchToGear(Mode_FuckDog);
				  break;
				case 6:
				  //在四击没有配置为夜行模式的时候6击进入。
				  if(!QuadClickSel)SwitchToGear(Mode_FuckDog);
				  break;
				case 7:
					//7击进入设置菜单
					TriggerSetupMenuDisplay();
				  break;
				case 8:
					//在电池电量高于指定放电阈值时，8击进入放电模式
					if(CellVoltage>DischargeThres)
						{
						SwitchToGear(Mode_Discharge);
						IsBatteryNearDrained=0;         //进入放电模式并clear标志位
						}
				  else LEDMode=LED_RedBlinkFifth;   //电池电量不足以开启，红灯闪五下提示
				  break;
				//其余情况什么都不做
        default:break;				
				}
			//长按开机进入月光挡位	
      if(getSideKeyLongPressEvent())EnterMoonProcess();				
		  //N击+长按查询电压，温度和进入1流明挡位
			ProcessNClickAndHoldHandler();
  		break;
		//出现错误	
		case Mode_Fault:
      SysMode=Operation_Normal; //故障后自动回到普通模式	
		  if(IsErrorFatal())
				{
				//电池已经耗尽，强制关闭并且禁止开机
				if(IsBatteryFault)IsDisplayLocked=0;
				//在NTC故障状态下可以应急开机使用，但是锁50mA，不准换挡允许用户应急使用
				else if(ErrCode==Fault_NTCFailed&&ClickCount)IsDisplayLocked=~IsDisplayLocked;
				}				 
			//非致命错误状态用户按下按钮清除错误，清除后特殊功能模块会让主灯熄灭
			else if(getSideKeyLongPressEvent())ClearError();
		  break;
		 //月光状态
		 case Mode_Moon:
			 //电池电压充足，长按进入低亮挡位
		   if(!IsSwitchingKeyStillHold&&getSideKeyLongPressEvent())  
					{
					PowerToNormalMode(Mode_ExtremelyLow); //开机到极低亮模式
					if(CurrentMode->ModeIdx==Mode_Moon)break;//换挡之后无法成功离开月光模式，不进行下面的复位操作
					if(IsRampEnabled)LoadMinimumRampCurrentToRAM(); //如果是无极调光则恢复到最低电流
					PauseHoldSwitchGear(); //禁止换挡系统工作
					}		    	
		//1流明挡位						
	  case Mode_1Lumen:
			 /***********************************************
		   月光和1LM模式按键灯亮度减半
		   （这里利用了switch语句的shoot through特性，执行
			 正常月光之后没有break所以会往下走跳到1LM的位置
			 执行设置按键灯亮度一半的处理）
		   ***********************************************/
			 IsHalfBrightness=1; 
		   if(CellVoltage<2050)ReturnToOFFState();   //单节电池电压小于2.05（四节电池一共8.21V）之后DCDC可能工作异常，强制断电
			 break;				
    //无极调光状态				
    case Mode_Ramp:
		    RampLowVoltHandler(); 				//低电压保护
        RampAdjHandler();					    //无极调光处理
		    break;
		//极亮状态
    case Mode_Turbo:
				TurboLVILIMProcess(); //执行极亮低电流检测
			  if(ClickCount==2||IsForceLeaveTurbo)PowerToNormalMode(Mode_Low); //双击或者温度达到上限值，强制返回到低亮
				if(ClickCount==3)SwitchToGear(LastSpecialMode); //侧按3击进入上次关闭的特殊功能组
		    break;	
		//特殊功能挡位（爆闪、SOS、信标）执行退出检测
    case Mode_Strobe:		
		case Mode_SOS:
		case Mode_Beacon:
			  //开机状态下二击或者三击执行退出挡位记忆判断
			  if(IsLargerThanOneU8(ClickCount)&&!IsLargerThanThreeU8(ClickCount))SpecialModeMemoryHandler();
		    //执行实际的特殊模式退出操作
				if(ClickCount==3)PowerToNormalMode(LastMode); //三击调用退回函数，退回到普通模式
				else TryEnterTurboStrobeProcess(ClickCount); //其他按键次数，直接call尝试极亮函数让他自己判断去
		    break;				
		}
		
	//处理FSM中的表驱动部分
	if(ModeBeforeFSMSwitch==CurrentMode->ModeIdx)
		{
		//如果状态机FSM内有操作或者当前处于版本检查状态则跳过表驱动，否则执行表驱动
		ModeSwitchFSMTableDriver(ClickCount); 
		}
	ClearShortPressEvent(); //表驱动事项响应完毕，清除按键状态
  }

//应用输出电流参数
void ApplyOutputCurrent(void)
	{
	//默认关闭高频爆闪增强Halt
	IsHighPowerStrobe=0;
	//应用输出电流
	if(DisplayLockedTIM||IsDisplayLocked)Current=CalcIREFValue(50); //用户进入或者退出锁定，用50mA短暂点亮提示一下
	else switch(CurrentMode->ModeIdx)	
		{ 
		//极亮模式
    case Mode_Turbo:
		  Current=QuerySystemFullScaleCurrent();  //ECO模式开启时使用ECO电流，否则使用极亮电流
      if(TurboILIM<Current)Current=TurboILIM; //应用限流设置
		  //极亮模式温控始终开启
		  IsPauseThermalCalc=0;
		  break;
		//信标模式
		case Mode_Beacon:
			switch(BeaconFSM())
				 {
				 case 0:Current=-1;break; //0表示让电流关闭
				 case 2:Current=CalcIREFValue(200);break; //用200mA低亮提示告知用户已进入信标模式
				 default:SpecialModeCurrentFetch(); //其他值调用系统默认电流
				 } 	
			 //信标模式下温控始终开启
       IsPauseThermalCalc=0;		 
			 break;
		//SOS模式	
		case Mode_SOS: 
			 if(!SOSFSM())
				 {
				 //SOS模式需要熄灭LED，温控关闭
				 IsPauseThermalCalc=1;
				 Current=-1;
				 }
			 else 
				 {
				 //点亮LED，温控开启
				 IsPauseThermalCalc=0;
				 SpecialModeCurrentFetch();
				 }
			 break;
		//操远光狗模式		 
	  case Mode_FuckDog:
			 if(getSideKey1HEvent())
				{
				//单击+长按暂时熄灭手电避免晃到对面
				IsPauseThermalCalc=1;
				Current=-1;
				break;
				}
			 else if(!getSideKeyHoldEvent())
				{
				//默认情况，手电取最小电流常亮
				IsPauseThermalCalc=1;
				Current=CurrentMode->MinCurrent;
				
				/***********************************************************
				这里又利用了case的shoot through特性，如果按键持续按下，会跳过
				这一段代码中的break然后直接shoot到下面执行爆闪逻辑，这样就起到
				了长按爆闪的效果。
				***********************************************************/
				break;
				}		
	  //爆闪模式
		case Mode_Strobe:     
			 //爆闪模式温控始终开启
			 IsPauseThermalCalc=0;
		   IsHighPowerStrobe=1;                   //进入爆闪模式，开启高Halt提高斜率
       if(!StrobeOutputHandler())Current=-1; 
		   else SpecialModeCurrentFetch();
		   break;
	  //关机状态下电流缓降
		case Mode_OFF:	
			 //关机状态电流缓降，停止温控计算
			 IsPauseThermalCalc=1;
       //关机函数没有使能该功能或者拖尾被用户禁用，电流直接到0			
       if(!SysCfg.FadingCfg||!IsSlowFading)Current=0; 
		   //逐渐变暗特效开启，缓慢减少电流
			 else if(Current>CalcIREFValue(20))Current-=1+(Current/(((int)SysCfg.FadingCfg)*430));
 		   else IsSlowFading=0;		//特效结束，清除flag并使得电流置零
			 break;
		
		//放电模式	
		case Mode_Discharge:
			//电池耗尽后切换到指定挡位，设置电流到最小值
			if(IsBatteryNearDrained)
				{			
				/***********************************************************
				这里又利用了case的shoot through特性，如果没用触发电池耗尽，则
				这一段代码中的break会被跳过，然后直接shoot到下面执行正常输出电
				流的逻辑，这样就起到了电池电压充足时直接按照设计电流点亮的效果
				***********************************************************/
				Current=CurrentMode->MinCurrent;
				break;
				}
		  //电池接近耗尽后切换到指定挡位，确保没有电压差能把电池完全放空
		  else if(CellVoltage<(DischargeThres+75))IsBatteryNearDrained=1;	
				
		//其余模式，电流取正常值
		default:
			//默认温控始终开启
			IsPauseThermalCalc=0;
		  //计算电流值
		  if(LowPowerStrobe())Current=-1; //触发低压报警，闪烁
			else if(CurrentMode->ModeIdx==Mode_Ramp)
				{
				//无极调光模式取结构体内数据
				if(SysCfg.RampCurrent>SysCfg.RampCurrentLimit)Current=SysCfg.RampCurrentLimit;
				else Current=SysCfg.RampCurrent;
				}
		  else Current=QueryCurrentGearILED(); //其他挡位使用设置值作为目标电流
		}				
	//无极调光模式指示(无极调光模式在抵达上下限后短暂熄灭或者调到25%)
	if(SysCfg.RampLimitReachDisplayTIM)Current=IsNotifyMaxRampLimitReached?Current>>2:-1;
	}	

/*********************************  End Of File  ************************************/
