redstoner-35/DFEx-FloodBeaMon3tr/固件/禁赛级风扇手柄固件源码/Hardware/PWM.c

/****************************************************************************/
/** \file PWM.c
/** \Author redstoner_35
/** \Project Xtern Ripper Hyper Fan Ultra Edition
/** \Description 这个文件负责驱动系统的ePWM模块对外提供风扇调速信号和PWMDAC模拟
								 输出完成恒压注入实现电压调速功能。
**
**	History:
				2026年9月11日 Initial Release
**	
*****************************************************************************/
/****************************************************************************/
/*	include files
*****************************************************************************/
#include "cms8s6990.h"
#include "PinDefs.h"
#include "GPIO.h"
#include "PWMCfg.h"

/****************************************************************************/
/*	Local pre-processor symbols/macros('#define') For Parameter definition
****************************************************************************/
#define SysFreq 48000000 //系统时钟频率(单位Hz)
#define PWMFreq 6000 //PWM频率(单位Hz)	
#define FanPWMFreq 20000	//风扇的PWM频率(单位Hz)	
	
/****************************************************************************/
/*	Local pre-processor symbols/macros('#define') For Parameter parsing

Note: 以下的宏请勿修改，否则会导致PWM模块工作异常！
****************************************************************************/
#define PWMStepConstant (SysFreq/PWMFreq)-1 				
#define FanPWMStepConstantVal (SysFreq/FanPWMFreq)-1  //PWM周期自动定义

//PWM使能操作
#define PWM_Enable() 	do{PWMFBKC=0x00;PWMCNTE=0x11;}while(0) //使能PWM输出 

/****************************************************************************/
/*	Global variable definitions(declared in header file with 'extern')
****************************************************************************/
xdata float CVDACTargetDuty;
xdata unsigned int FanPWMDuty; //风扇和恒压DAC的目标占空比
bit IsNeedToUploadPWM; 				 //是否需要更新PWM

/****************************************************************************/
/*	Local variable and special Register definitions('static')
****************************************************************************/
static bit IsPWMLoading; //PWM正在加载中
static bit IsNeedToEnableOutput; //是否需要启用输出
static bit IsNeedToEnableMOS; //是否需要使能MOS管

sbit FanPWMPin=FanPWMIOP^FanPWMIOx;
sbit CVDACPin=CVDACIOP^CVDACIOx;

/****************************************************************************/
/* Global Function implementation - Initialization
****************************************************************************/	

//关闭PWM定时器
void PWM_DeInit(void)
	{
	//配置为普通GPIO
	GPIO_SetMUXMode(FanPWMIOG,FanPWMIOx,GPIO_AF_GPIO);
  GPIO_SetMUXMode(CVDACIOG,CVDACIOx,GPIO_AF_GPIO);
	//关闭PWM模块
	PWMCNTCLR=0x11; //复位PWM0和4的计数器
	PWMOE=0x00;
	PWMCNTE=0x00;		//关闭PWM计数器
	PWM45PSC=0x00;
	PWM01PSC=0x00;  //关闭PWM分频器时钟
	}

//上传PWM值
static void UploadPWMValue(void)	
	{
	PWMLOADEN=0x11; //加载通道0的PWM值
	while(PWMLOADEN&0x11); //等待加载结束
	}
		
//PWM定时器初始化
void PWM_Init(void)
	{
	GPIOCfgDef PWMInitCfg;
	//设置结构体
	PWMInitCfg.Mode=GPIO_Out_PP;
  PWMInitCfg.Slew=GPIO_Fast_Slew;		
	PWMInitCfg.DRVCurrent=GPIO_High_Current; //推FanPWM，不需要很高的上升斜率
	//配置GPIO
	CVDACPin=0;
  FanPWMPin=0; 				//令FanPWM的输出在非PWM模式下始终输出0
	GPIO_ConfigGPIOMode(CVDACIOG,GPIOMask(CVDACIOx),&PWMInitCfg); 
	GPIO_ConfigGPIOMode(FanPWMIOG,GPIOMask(FanPWMIOx),&PWMInitCfg); 
	//配置PWM发生器
	PWMCON=0x00; 		//PWM通道为六通道独立模式，向下计数，关闭非对称计数功能	
	PWMOE=0x11; 		//打开PWM输出通道0和4
	PWM01PSC=0x01;  
	PWM45PSC=0x01;  //打开预分频器和计数器时钟 
  PWM0DIV=0xff;   
	PWM4DIV=0xff;   //令Fpwmcnt=Fsys=48MHz(不分频)
  PWMPINV=0x00; 	//所有通道均设置为正常输出模式
	PWMCNTM=0x11; 	//通道0和4配置为自动加载模式
	PWMCNTCLR=0x11; //初始化PWM的时候复位通道0和4的定时器
	PWMDTE=0x00; 		//关闭死区时间
	PWMMASKD=0x00; 
	PWMMASKE=0x11; 	//PWM掩码功能启用，默认状态下禁止通道0和4输出
	//配置周期数据
	PWMP0H=(PWMStepConstant>>8)&0xFF;
	PWMP0L=PWMStepConstant&0xFF;	
	PWMP4H=(FanPWMStepConstantVal>>8)&0xFF;
	PWMP4L=FanPWMStepConstantVal&0xFF;
	//配置占空比数据
  PWMD0H=0;
  PWMD4H=0x0;
	PWMD0L=0;	
	PWMD4L=0x0;
	//初始化变量
	CVDACTargetDuty=0;
	FanPWMDuty=0;
	IsPWMLoading=0; 
	IsNeedToUploadPWM=0;
	//启用PWM
	PWM_Enable();
	UploadPWMValue();	
	//PWM初始化完毕，将引脚启用为复用功能
	GPIO_SetMUXMode(FanPWMIOG,FanPWMIOx,GPIO_AF_PWMCH4);
  GPIO_SetMUXMode(CVDACIOG,CVDACIOx,GPIO_AF_PWMCH0);
	}

/****************************************************************************/
/* Global Function implementation - Special Operation
****************************************************************************/		
	
//获取风扇PWM的数值常量
int FanPWMStepConstant(void)
	{
	/*****************************************************
	特殊的函数，返回一个常量值供原来获取PWM常量的函数进行运算
	将硬件底层的参数宏和上层应用调用隔离。	
		
	这里不用担心函数返回的开销，因为编译器检测到这个函数只返
	回一个宏定义的常量，内部没有其他任何操作的话就不会生成函
	数进入和返回的入栈压栈和RETI代码。
	*****************************************************/
	return FanPWMStepConstantVal;
	}
	
/****************************************************************************/
/* Global Function implementation - Logic Handler
****************************************************************************/	

//根据PWM结构体内的配置进行输出
void PWM_OutputCtrlHandler(void)	
	{
	int value;
	float buf;
	//当前系统未请求加载
	if(!IsNeedToUploadPWM)return; //不需要加载
	//当次加载已开始，进行结束监测
	else if(IsPWMLoading) 
		{
	  if(PWMLOADEN&0x11)return;//加载寄存器复位为0，表示加载成功
	  //加载结束
		if(IsNeedToEnableMOS)PWMMASKE&=0xEF;
		else PWMMASKE|=0x10;
		if(IsNeedToEnableOutput)PWMMASKE&=0xFE;
		else PWMMASKE|=0x01;   //更新PWMMASKE寄存器根据输出状态启用对应的通道
		IsNeedToUploadPWM=0;
		IsPWMLoading=0;  //正在加载状态为清除
		}
	//当次加载已被请求开始，进行加载处理
	else
		{
		//PWM占空比参数限制
		if(CVDACTargetDuty>100)CVDACTargetDuty=100;
		if(CVDACTargetDuty<0)CVDACTargetDuty=0;
		if(FanPWMDuty>FanPWMStepConstantVal)FanPWMDuty=FanPWMStepConstantVal;
		//根据PWM数值选择MASK寄存器是否启用
		IsNeedToEnableOutput=CVDACTargetDuty>0?1:0; //是否需要启用输出
		IsNeedToEnableMOS=FanPWMDuty?1:0;  //配置是否需要使能FET
		//配置寄存器装载CV DAC的PWM设置数值
		buf=CVDACTargetDuty*(float)PWMStepConstant;
		buf/=(float)100;
		value=(int)buf;
		PWMD0H=(value>>8)&0xFF;
		PWMD0L=value&0xFF;		
		//装载风扇的PWM数值
		value=FanPWMStepConstantVal-FanPWMDuty;  //因为风扇PWM电路的输出电平位移自带反相器所以需要输出反过来的占空比
		if(!value)IsNeedToEnableMOS=0; //PWM输出100%的时候直接让输出MOS关掉就行了
		PWMD4H=(value>>8)&0xFF;
		PWMD4L=value&0xFF;			
		//PWM寄存器数值已装入，应用数值		
		IsPWMLoading=1; //标记加载过程进行中
		PWMLOADEN|=0x11; //开始加载
		}
	}
/*****************************  End Of File  ******************************/
