redstoner-35/DFEx-FloodBeaMon3tr/固件/禁赛级风扇手柄固件源码/Logic/BattVoltDisplay.c

/****************************************************************************/
/** \file BattVoltDisplay.c
/** \Author redstoner_35
/** \Project Xtern Ripper Hyper Fan Ultra Edition
/** \Description 这个文件是上层应用层逻辑，负责实现系统的电池和温度报告，电池低
								 电量降档和关机保护以及电量显示的指示灯控制等逻辑。
**	History:
				2026年9月11日 Initial Release
**	
*****************************************************************************/
/****************************************************************************/
/*	include files
*****************************************************************************/
#include "ADCCfg.h"
#include "LEDMgmt.h"
#include "delay.h"
#include "SideKey.h"
#include "BattDisplay.h"
#include "FastOp.h"
#include "OutputChannel.h"
#include "ModeSel.h"
#include "SysConfig.h"
#include "SysReset.h"


/****************************************************************************/
/*	Local pre-processor symbols/macros('#define') For Parameter definition
****************************************************************************/

//等效单节电池电压数据的平均次数(用于内部逻辑的低压保护,电量显示和电量不足跳档)
#define VBattAvgCount 40 

/****************************************************************************/
/*	Local type definitions('typedef')
*****************************************************************************/

//电池电压平均计算结构体声明
typedef struct
	{
	int Min;
  int Max;
	long AvgBuf;
	unsigned char Count;
	}AverageCalcDef;	

typedef enum
	{
  BattVdis_Waiting, //等待显示阶段
	BattVdis_PrepareDis, //准备显示
	BattVdis_DelayBeforeDisplay, //延迟一段时间
	BattVdis_Show10V, //显示十位
	BattVdis_Gap10to1V, //十位和个位之间的等待
	BattVdis_Show1V, //显示个位
	BattVdis_Gap1to0_1V, //个位和十分位之间的等待
	BattVdis_Show0_1V, //显示小数点后一位(0.1V)
	BattVdis_WaitShowChargeLvl, //等待一段时间后显示当前电量
	BattVdis_ShowChargeLvl, //显示电池电量的等待
	BattVdis_WaitShowTempState,
	BattVdis_ShowTempState	
	}BattVshowFSMDef; //电池电量显示处理	
	
/****************************************************************************/
/*	Global variable definitions(declared in header file with 'extern')
****************************************************************************/
bit IsBatteryAlert; //电池电压低于警告值	
bit IsBatteryFault; //电池电压低于保护值		
xdata int CellVoltage; //等效单节电池电压
xdata unsigned char CommonSysFSMTIM;  //电压显示计时器


/****************************************************************************/
/*	Local variable definitions('static')
****************************************************************************/
static xdata unsigned char BattShowTimer=0; //电池电量显示计时
static xdata unsigned char OneLMShowBattStateTimer=0; //1LM模式下显示电池状态的计时器
static xdata AverageCalcDef BattVolt;	
static xdata int VbattSample; //取样的电池电压
static xdata BattStatusDef BattState; //电池电量标记位
static bit IsReportingTemperature=0; //报告温度
static xdata BattVshowFSMDef VshowFSMState; //电池电压显示所需的计时器和状态机转移

/****************************************************************************/
/*	Local constant definitions('static code',Stored in Code ROM)
****************************************************************************/
//内部使用的先导显示表
static code LEDStateDef VShowIndexCode[]=
	{
	LED_Red,
	LED_Amber,
	LED_Green,  //正常过渡是红黄绿
	LED_Amber,
	LED_Red  		//高精度模式是反过来，绿红黄
	};

/****************************************************************************/
/* Local Function implementation - Battery State Report FSM & Avg Related
****************************************************************************/	

//复位电池电压检测缓存
static void ResetBattAvg(void)	
	{
	BattVolt.Min=32766;
	BattVolt.Max=-32766; //复位最大最小捕获器
	BattVolt.Count=0;
  BattVolt.AvgBuf=0; //清除平均计数器和缓存
	}	
	
//根据电池状态机设置LED指示电池电量
static void SetPowerLEDBasedOnVbatt(void)	
	{
	switch(BattState)
		{
		 case Battery_Plenty:LEDMode=LED_Green;break; //电池电量充足绿色常亮
		 case Battery_Mid:LEDMode=LED_Amber;break; //电池电量中等黄色常亮
		 case Battery_Low:LEDMode=LED_Red;break;//电池电量不足
		 case Battery_VeryLow:LEDMode=LED_RedBlink;break; //电池电量严重不足红色慢闪
		}
	}
	
//电池电量状态机
static void BatteryStateFSM(void)
	{
	xdata int Thres;
	xdata float buf;
	//计算转灯阈值
	if(TargetfanSpeed<(float)20)buf=0;
  buf=TargetfanSpeed-(float)20;                  //计算风扇速度和目标的Δ值		
	buf=(float)3700-((float)300*(buf/(float)80));  //阈值变化数值=(风扇速度Δ值/风扇速度变化范围的总值)*电压变化的总阈值,并计算出最终转黄灯阈值（3700-Δ量）
  Thres=(int)buf;
	//状态机处理	
	switch(BattState) 
		 {
		 //电池电量充足
		 case Battery_Plenty: 
				if(CellVoltage<Thres)BattState=Battery_Mid; //电池电压小于3.7V，回到电量中等状态
			  break;
		 //电池电量较为充足
		 case Battery_Mid:
			  if(CellVoltage>(Thres+200))BattState=Battery_Plenty; //电池电压大于阈值，回到充足状态
				if(CellVoltage<(Thres-200))BattState=Battery_Low; //电池电压低于阈值则切换到电量低的状态
				break;
		 //电池电量不足
		 case Battery_Low:
		    if(CellVoltage>Thres)BattState=Battery_Mid; //电池电压高于3.6，切换到电量中等的状态
			  if(CellVoltage<2950)BattState=Battery_VeryLow; //电池电压低于2.95，报告严重不足
		    break;
		 //电池电量严重不足
		 case Battery_VeryLow:
			  if(CellVoltage>(Thres-200))BattState=Battery_Low; //电池电压回升到指定阈值，跳转到电量不足阶段
		    break;
		 }
	}
	
/****************************************************************************/
/* Local Function implementation - Temperature & Voltage Report FSM
****************************************************************************/		
	
//电池采样显示电压
static LEDStateDef VshowEnter_ShowIndex(void)
	{
	char Index;
	if(CommonSysFSMTIM>9)
		{
		Index=((CommonSysFSMTIM-8)>>1)-1;
		if(IsReportingTemperature&&!IsNegative16(Data.Systemp))Index+=2; //温度播报时温度为正数，使用常规显示模式
		if(!IsReportingTemperature&&VbattSample>999)Index+=2; 		//电压播报时传入电压大于10V,使用常规显示模式
		return VShowIndexCode[Index];
		}
	return LED_OFF; //红黄绿闪烁之后(如果是高精度显示模式则为绿红黄)等待
	}	
	
//控制LED侧按产生闪烁指示电池电压的处理
static void VshowGenerateSideStrobe(LEDStateDef Color,BattVshowFSMDef NextStep)
	{
	//传入的是负数，符号位=1，通过快闪一次表示是0
	if(IsNegative8(CommonSysFSMTIM))
		{
		MakeFastStrobe(Color);
		CommonSysFSMTIM=0; 
		}
	//正常指示
	LEDMode=(CommonSysFSMTIM%4)&0x7E?Color:LED_OFF; //制造红色闪烁指示对应位的电压
	//显示结束
	if(!CommonSysFSMTIM) 
		{
		LEDMode=LED_OFF;
		CommonSysFSMTIM=10;
		VshowFSMState=NextStep; //等待一会
		}
	}
//电压显示状态机根据对应的电压位数计算出闪烁定时器的配置值
static void VshowFSMGenTIMValue(int Vsample,BattVshowFSMDef NextStep)
	{
	if(!CommonSysFSMTIM)	//时间到允许配置
		{	
		if(!Vsample)CommonSysFSMTIM=0x80; //0x80=瞬间闪一下
		else CommonSysFSMTIM=(4*Vsample)-1; //配置显示的时长
		VshowFSMState=NextStep; //执行下一步显示
		}
	}	

//电池详细电压显示的状态机处理
static void BatVshowFSM(void)
	{
		//电量显示状态机
	switch(VshowFSMState)
		{
		case BattVdis_PrepareDis: //准备显示
			if(CommonSysFSMTIM)break;
	    CommonSysFSMTIM=15; //延迟1.75秒
			VshowFSMState=BattVdis_DelayBeforeDisplay; //显示头部
		  break;
		//延迟并显示开头
		case BattVdis_DelayBeforeDisplay: 
			//头部显示结束后开始正式显示电压
			LEDMode=VshowEnter_ShowIndex();
		  if(CommonSysFSMTIM)break;
			//电池电压为大于10V的数，进行四舍五入处理保留小数点后一位的结果
		  if(VbattSample>999)
			   {
				 /********************************************************
				 这里四舍五入的原理是电池电压会被采样为整数，1LSB=0.01V。例如
				 电池电压为12.59V采样之后就会变成1259。那么此时我们需要对小数
				 点后两位进行四舍五入判断，得到一位小数的结果。由于整数结果的
				 个位实际上等于浮点的电池电压中的小数点后两位，因此我们只需要
				 通过和10求余数就可以取出小数点后结果的2位，然后如果结果大于4
				 则进行进位，令小数点后一位+1就实现了四舍五入了。对整个采样结
				 果除以10之后就会自动去掉小数点后两位的值保留1位小数。
				 *********************************************************/					 
				 if((VbattSample%10)>4)VbattSample+=10;
				 VbattSample/=10;
				 }
			//配置计时器显示第一组电压
			VshowFSMGenTIMValue(VbattSample/100,BattVdis_Show10V);
		  break;
    //显示十位
		case BattVdis_Show10V:
			VshowGenerateSideStrobe(LED_Red,BattVdis_Gap10to1V); //调用处理函数生成红色侧部闪烁
		  break;
		//十位和个位之间的间隔
		case BattVdis_Gap10to1V:
			VbattSample%=100;
			VshowFSMGenTIMValue(VbattSample/10,BattVdis_Show1V); //配置计时器开始显示下一组	
			break;	
		//显示个位
		case BattVdis_Show1V:
		  VshowGenerateSideStrobe(LED_Amber,BattVdis_Gap1to0_1V); //调用处理函数生成黄色侧部闪烁
		  break;
		//个位和十分位之间的间隔		
		case BattVdis_Gap1to0_1V:	
			//温度播报结束之后直接进入等待阶段
			if(IsReportingTemperature)
				{
				CommonSysFSMTIM=10;  
				VshowFSMState=BattVdis_WaitShowTempState; 
				}
			else VshowFSMGenTIMValue(VbattSample%10,BattVdis_Show0_1V);
			break;
		//显示小数点后一位(0.1V)
		case BattVdis_Show0_1V:
		  VshowGenerateSideStrobe(LED_Green,BattVdis_WaitShowChargeLvl); //调用处理函数生成绿色侧部闪烁
			break;
		//等待一段时间后显示当前温度水平
		case BattVdis_WaitShowTempState: 
			if(CommonSysFSMTIM)break;
			VshowFSMState=BattVdis_ShowTempState;
		  CommonSysFSMTIM=31;
			break;
	 
		//等待当前温度水平显示结束
		case BattVdis_ShowTempState:
			if(CommonSysFSMTIM<25&&CommonSysFSMTIM&0xF8)
				{
				if(Data.Systemp<47)LEDMode=LED_Green;
				else if(Data.Systemp<56)LEDMode=LED_Amber;
				else LEDMode=LED_Red;
				}
			//显示结束，LED熄灭一段时间
			else LEDMode=LED_OFF;
			//等待温度状态显示时间到，到了之后跳转到等待用户松开按键的处理
			if(!CommonSysFSMTIM)VshowFSMState=BattVdis_ShowChargeLvl;
			break;		  
		//等待一段时间后显示当前电量
		case BattVdis_WaitShowChargeLvl:
			if(CommonSysFSMTIM)break;
			//1LM模式以及关机下电量指示灯不常驻点亮，所以需要额外给个延时让LED点亮
			if(CurrentMode->ModeIdx==Mode_OFF)BattShowTimer=18; 
			VshowFSMState=BattVdis_ShowChargeLvl; //等待电量显示状态结束
      break;
	  //等待总体电量显示结束
		case BattVdis_ShowChargeLvl:
			IsReportingTemperature=0;  									//clear掉温度显示标志位
			VbattSample=0;                              //电压显示每次结束后，clear掉电压缓存数据
		  if(BattShowTimer)SetPowerLEDBasedOnVbatt();//显示电量
			else if(!getSideKeyNClickAndHoldEvent())VshowFSMState=BattVdis_Waiting; //用户仍然按下按键，等待用户松开,松开后回到等待阶段
      break;
		}
	}	

/****************************************************************************/
/* Global Function implementation - API For Trigger Batt/Temp Status report
****************************************************************************/	
	
//触发电池电量提示
void TriggerBattStatDisplay(void)
	{
  //电量显示进行中不允许操作
	if(BattShowTimer)return;
	//设置定时器，启动显示
	BattShowTimer=14;
	}	
	
//启动电池电压显示
void TriggerVshowDisplay(void)	
	{
	if(VshowFSMState!=BattVdis_Waiting)return; //非等待显示状态禁止操作
	VshowFSMState=BattVdis_PrepareDis;	
	if(GetIfFanOutputEnabled())
		{
		if(LEDMode!=LED_OFF)CommonSysFSMTIM=8; //指示灯点亮状态查询电量，熄灭LED等一会
		LEDMode=LED_OFF;
		}	
	IsReportingTemperature=0; //电压报告模式
	//进行电压取样(缩放为LSB=0.01V)
	VbattSample=(int)(Data.RawBattVolt*100); 		
	}		

//启动系统温度显示
void TriggerTShowDisplay(void)
	{
	if(!Data.IsNTCOK||VshowFSMState!=BattVdis_Waiting)return; //非等待显示状态禁止操作
	//准备显示状态机
	VshowFSMState=BattVdis_PrepareDis;	
	if(GetIfFanOutputEnabled())
		{
		if(LEDMode!=LED_OFF)CommonSysFSMTIM=8; //指示灯点亮状态查询电量，熄灭LED等一会
		LEDMode=LED_OFF;
		}	
	IsReportingTemperature=1; //温度报告模式	
	//进行温度取样
	if(IsNegative16(Data.Systemp))VbattSample=(int)Data.Systemp*-10;
	else VbattSample=(int)Data.Systemp*10;
	}
	
//查询函数，电压提示状态机是否在操作
bit	IsVshowFSMInAction(void)
	{
	return VshowFSMState!=BattVdis_Waiting?1:0;
	}

/****************************************************************************/
/* Global Function implementation - Initialization
****************************************************************************/	

//等待电池电压就绪（安全保护）
void WaitBatteryVoltageOK(void)
	{
	unsigned char Wait=200;
	do
		{		
		//延迟10mS采样电池电压
		delay_ms(10);
		SystemTelemHandler();
		//如果电池电压正常则退出
		if(Data.RawBattVolt>2.50)return;
		}
	while(--Wait);
	//电池电压不正常，禁止固件启动并亮红灯
	LEDMode=LED_Red;
	while(1)LEDControlHandler();
	}		

//在启动时显示电池电压
void DisplayVBattAtStart(bit IsPOR)
	{
	unsigned char i=10;
	//初始化平均值缓存,复位标志位
	ResetBattAvg();
  //复位电池电压状态和电池显示状态机
  VshowFSMState=BattVdis_Waiting;		
	do
		{
		SystemTelemHandler();
		CellVoltage=(int)(Data.BatteryVoltage*1000); //获取并更新电池电压
		BatteryStateFSM(); //反复循环执行状态机更新到最终的电池状态
		}
	while(--i);
	//启动电池电量显示(仅系统使能的情况下)
	if(!IsPOR)return;
	BattShowTimer=18; //使能电量提示计时器
	if(IsEnable2SMode)	
		{
		//2S模式激活，令指示灯以黄色快闪两次指示开启2S模式
		MakeFastStrobe(LED_Amber);
		delay_ms(200);
		MakeFastStrobe(LED_Amber);
		//两次闪烁后延迟半秒再继续接下来的流程
		for(i=48;i;i--)delay_ms(10); 
		}
	
	}
	
/****************************************************************************/
/* Global Function implementation - Logic Handler for Battery telemetry
****************************************************************************/		
	
//电池参数测量和指示灯控制
void BatteryTelemHandler(void)
	{
	//根据电池电压控制flag实现低电压降档和关机保护
  if(CellVoltage>2820)		
		{
		if(IsBatteryFault)
			{
			//故障bit置起，令警告bit始终=0，并且检测直到电池电压回升到足以解除的等级后clear掉故障flag
			if(CellVoltage>3000)IsBatteryFault=0;
			IsBatteryAlert=0;
			}
		else IsBatteryAlert=CellVoltage>CurrentMode->LowVoltThres?0:1; //警报bit根据各个挡位的阈值进行判断
		}
	else
		{
		IsBatteryAlert=0; //故障bit置起后强制清除警报bit
		IsBatteryFault=1; //故障bit=1
		}
	//电池电量指示状态机
	BatteryStateFSM();
	//LED控制
	if(IsOneTimeStrobe())return; //为了避免干扰只工作一次的频闪指示，不执行控制 
	else if(VshowFSMState!=BattVdis_Waiting)BatVshowFSM();//电池电压显示启动，执行状态机
	else if((GetIfFanOutputEnabled()&&CurrentMode->ModeIdx!=Mode_OFF)||BattShowTimer)
		{
		//用户查询电量或者风扇手柄开机，指示电量
		SetPowerLEDBasedOnVbatt(); 
		}
  else LEDMode=LED_OFF; //风扇手柄处于关闭状态，且没有按键按下的动静，故LED设置为关闭
	}

//电池电量显示延时的处理
void BattDisplayTIM(void)
	{
	long buf;
	//电量平均模块计算
	if(BattVolt.Count<VBattAvgCount)		
		{
		buf=(long)(Data.BatteryVoltage*1000);
		BattVolt.Count++;
		BattVolt.AvgBuf+=buf;
		if(BattVolt.Min>buf)BattVolt.Min=buf;
		if(BattVolt.Max<buf)BattVolt.Max=buf; //极值读取
		}
	else //平均次数到，更新电压
		{
		BattVolt.AvgBuf-=(long)BattVolt.Min+(long)BattVolt.Max; //去掉最高最低
		BattVolt.AvgBuf/=(long)(BattVolt.Count-2); //求平均值
		CellVoltage=(int)BattVolt.AvgBuf;	//得到最终的电池电压(单位mV)
		ResetBattAvg(); //复位缓存
		}
	//电池电压显示的计时器处理	
	if(CommonSysFSMTIM)CommonSysFSMTIM--;
	//电池显示定时器
	if(BattShowTimer)BattShowTimer--;
	}

/****************************************************************************/
/* Function implementation - Handler for cell count detection
****************************************************************************/	

//没有配置锁的电池检测
static void CellCountNoCfgLock(void)
	{
	unsigned char delay;
	extern bit IsEnablePWMFan;
	
	#ifdef EnableHyper1S		
	//初始化延时变量
	delay=0;   
	//开启暴力1S模式，强制锁定禁止2S工作
	if(!IsEnableBattCfgLock||IsEnable2SMode)
		{
		IsEnableBattCfgLock=1;
		IsEnable2SMode=0;
		SaveSysConfig(0); 
		TriggerSoftwareReset();
		}	
  //在非锁定模式下如果电池电压超过4.35则锁死
  if(Data.RawBattVolt>4.35)while(1)
		{
		delay_ms(15);
		delay=delay?0:1;
		LEDMode=delay?LED_Red:LED_Green;		
		LEDControlHandler();
		}	
  #message "1S Hyper output mode enabled.Cell select feature will remain disabled."
  #message "This firmware only works with PCB installed with 2.2uH inductor!"		
		
	#else	
		
	//2S模式开启但是非PWM模式，关闭2S模式并重启系统		
	if(IsEnable2SMode&&!IsEnablePWMFan)
		{
		IsEnable2SMode=0;
		SaveSysConfig(0); 
		TriggerSoftwareReset();
		}	
	//检测输入的电池电压是否超过额定的满电值，超过则触发保护锁死
	if(Data.RawBattVolt>(IsEnablePWMFan?8.60:4.35))while(1)	
		{
		//电池电压超过允许范围，则触发保护红绿快闪
		delay_ms(50);
		delay=delay?0:1;
		LEDMode=delay?LED_Red:LED_Green;		
		LEDControlHandler();
		}
	//2S模式关闭且电池电压大于4.35，打开2S模式
	else if(!IsEnable2SMode&&Data.RawBattVolt>4.35)
		{
		//启用2S模式	并更新配置
		IsEnable2SMode=1;
		SaveSysConfig(0); 	
		//制造绿色快闪表示更新到2S模式
		delay=40;
		do
			{
			LEDMode=delay&0x01?LED_Green:LED_OFF;
			delay_ms(40);
			LEDControlHandler();
			}
		while(--delay);
		//快闪结束后重启系统
		TriggerSoftwareReset();
		}
	
	#endif	
	}	
	
//检测电池电压并配置电池串数相关的保护逻辑
void BattCellCountConfig(void)
	{
	unsigned char Result=0;
	//测量一次系统电压和温度
	SystemTelemHandler();
	//检测到NTC故障，红黄绿交错闪，然后等待几秒反复重复
	if(!Data.IsNTCOK)while(1)
		{
		switch(Result)
			{
			case 0:LEDMode=LED_Red;break;
			case 1:LEDMode=LED_Amber;break;
			case 2:LEDMode=LED_Green;break;
			default:LEDMode=LED_OFF;
			}
		//执行灯珠控制
		delay_ms(100);
		LEDControlHandler();
		//计时变量自增实现交错显示
		Result=Result+1%10;  
		}
	
	//温度感测正常，默认电池OK
  Result=1;		
		
	//系统未锁定，允许根据模式自动更改
	if(!IsEnableBattCfgLock)CellCountNoCfgLock();
	//系统已锁定，根据配置执行检查
	else
		{
		//系统在非PWM调速模式下开启2S模式，配置不合法
		if(!IsEnablePWMFan&&IsEnable2SMode)Result=0;
		//系统在2S模式下输入超量电压，报异常
		else if(IsEnable2SMode&&Data.RawBattVolt>8.60)Result=0;
		//系统当前是1S，但是输入了2S的电压，判断为电池异常
		else if(!IsEnable2SMode&&Data.RawBattVolt>4.35)Result=0;
		}		
		
	//检测到电池异常，锁死并且红绿快闪报错
	if(!Result)while(1)	
		{
		delay_ms(15);
		Result=Result?0:1;
		LEDMode=Result?LED_Red:LED_Green;		
		LEDControlHandler();
		}	
	}	
/*****************************  End Of File  ******************************/
