redstoner-35/DFEx-FloodBeaMon3tr/固件/驱动固件源码/Logic/SpecialMode.c

/****************************************************************************/
/** \file SpecialMode.c
/** \Author redstoner_35
/** \Project Xtern Ripper Hyper Boost HV 4S-GaN Edition
/** \Description 这个文件为顶层应用层逻辑文件。该文件负责实现系统的非常规挡位
的进入以及退出逻辑，并且实现系统特殊模式（战术点亮、锁定等）的逻辑切换和显示

**	History: 

				2026年9月25日  14:11
														 1.调整进入极亮和爆闪之前的逻辑，调用挡位记忆模块进
															 行记录实现在系统开机状态直接双击极亮时进入双击前
															 的挡位。

        2026年9月14日  17:18 1.修改睡眠时间进入和退出函数，解决进入战术模式后因
															 睡眠时间未被重置而引起战术模式自动退出的故障。
				
				2025年12月26日 10:05 1.针对新增的日常走夜路模式调整战术模式的准入连击数
															 判定条件。改为根据配置文件自动判定。
				                     2.修改系统在锁定模式下的紧急月光逻辑，改为可以松手
															 持续运行，松手无操作后30秒自动熄灭。
														 3.允许用户在锁定模式下双击+长按查看系统当前电池电
															 压，便于长期放置时检查电量水平。
														 
				2025年12月20日 Initial Release
**	
*****************************************************************************/
/****************************************************************************/
/*	include files
*****************************************************************************/
#include "ModeControl.h"
#include "LEDMgmt.h"
#include "SideKey.h"
#include "BattDisplay.h"
#include "TempControl.h"
#include "SpecialMode.h"
#include "SysConfig.h"
#include "SideKey.h"
#include "LowVoltProt.h"
#include "sleep.h"

/****************************************************************************/
/*	Local pre-processor symbols/macros - for Parameter Definition
****************************************************************************/
#define EmergencyOFFModeTime 30

/****************************************************************************/
/*	Local variable and Flag definitions('static')
****************************************************************************/
static xdata unsigned char ShowTacModeTIM;  //显示极亮模式的计时器

/****************************************************************************/
/*	Global variable definitions(declared in header file with 'extern')
****************************************************************************/
bit IsDisplayLocked;							//标志位，指示系统锁定的时候按下按钮的动作
SpecialOperationDef SysMode; 			//系统模式

/****************************************************************************/
/*	Function implementation - local('static')
****************************************************************************/	

//进入退出锁定切换
static void EnterExitLock(void)
	{
	DisplayLockedTIM=8; //指示锁定状态切换
	SysMode=!SysMode?Operation_Locked:Operation_Normal;
	SaveSysConfig(0);
	ResetSleepTimer(); //进入和退出锁定，重置定时器避免系统异常
	}
	
//进入退出战术切换
static void EnterExitTac(void)
	{
	DisplayLockedTIM=2; //指示战术切换
	SysMode=!SysMode?Operation_TacTurbo:Operation_Normal;
	ResetSleepTimer();   //立即重置睡眠定时器，避免tac模式进入和退出后系统睡眠功能异常
	}	

/****************************************************************************/
/* Global	Function implementation - Logic Handler for entering 
	 Normal and Special Mode
****************************************************************************/		
	
//进入月光处理
void EnterMoonProcess(void)
	{
	//电池电压足够的时候进入月光
	if(CellVoltage>2800)SwitchToGear(Mode_Moon);
	//高于2.4V每节则进入1LM挡位
	else if(CellVoltage>2400)SwitchToGear(Mode_1Lumen);
	//电量已经低于DCDC可工作的水平，系统禁止开机并红色闪5次
	else LEDMode=LED_RedBlinkFifth; 
	}	

//开启到普通模式
void PowerToNormalMode(ModeIdxDef Mode)
	{
	if(CellVoltage>2900)SwitchToGear(IsRampEnabled?Mode_Ramp:Mode); //正常开启
	else if(CellVoltage>2650)EnterMoonProcess();  //电池电压大于2.7，执行进入月光判断    		
	else if(CurrentMode->ModeIdx==Mode_OFF)LEDMode=LED_RedBlinkFifth;	//手电处于关机状态下且电池电量不足，闪烁五次提示进不去	
	else ReturnToOFFState();	 //电池电量严重不足，且手电开着，直接关机
	//如果成功进入了无级模式，则进行复位处理
	if(CurrentMode->ModeIdx==Mode_Ramp)RampRestoreLVProtToMax();
	}
	
//尝试进入极亮和爆闪的处理
void TryEnterTurboStrobeProcess(unsigned char Count)	
	{
  switch(Count)
		{
		//双击极亮
		case 2:	
			//电池电量充足且没有触发关闭极亮的保护，正常开启
			if(CellVoltage>3450&&!IsDisableTurbo)
				 {
			   ModeMemoryHandler();        //进入之前覆写挡位记忆，保留进入之前的挡位
				 SwitchToGear(Mode_Turbo); 
				 }
			//电池电池电量不足或者极亮被锁定尝试开到高亮去
			else PowerToNormalMode(Mode_High);	
		  break;
	//三击爆闪
		case 3:
			//尝试进入爆闪（开机状态下进入上次记忆的特殊功能），如果电池电量不足则进入失败,电量指示五次闪烁
			if(CellVoltage>2700)
				{			
				//在开机状态下三击，记忆进入前的挡位并进入到上次退出之前的状态
				if(CurrentMode->ModeIdx!=Mode_OFF)
					{
				  ModeMemoryHandler();        																		//进入之前覆写挡位记忆，保留进入之前的挡位
					SwitchToGear(!IsSpecMemEnabled?Mode_Strobe:LastSpecialMode);
					}
				//关机状态下三击，一键爆闪
				else
					{
					IsStrobePoweredFromOFF=true;
					SwitchToGear(Mode_Strobe);
					}
				}
			//爆闪进入失败，LED闪五次提示
			else LEDMode=LED_RedBlinkFifth; 
		  break;
		}
	}

/****************************************************************************/
/* Global	Function implementation - Logic Handler & Mode Display for Special
	 Operating Mode(Tac or Lock Mode)
****************************************************************************/	
	
//显示战术模式启用
bit DisplayTacModeEnabled(void)
	{
	//计时器控制
	if(CurrentMode->ModeIdx!=Mode_OFF||SysMode<Operation_TacTurbo)ShowTacModeTIM=0;
	else //进行累加
		{
		ShowTacModeTIM++; //进行增加
		if(ShowTacModeTIM==14&&SysMode==Operation_TacStrobe)return 1; //战术爆闪模式激活，频闪2次
		else if(ShowTacModeTIM==16)
			{
			ShowTacModeTIM=0;
			return 1; //返回1打开显示
			}		
		}
	//其余状态返回0
	return 0;
	}	
	
//特殊功能切换处理（返回当前非0数值）
SpecialOperationDef SpecialModeOperation(unsigned char Click)
	{
		//特殊操作模式切换
		switch(SysMode)
			{
			//普通模式
			case Operation_Normal:
					if(Click==5)EnterExitLock(); //进入锁定模式
					if(Click==(QuadClickSel?6:4))EnterExitTac(); //系统开启四击进入战术模式
					break;
			//锁定模式
			case Operation_Locked:
				
					 //系统在查询电压阶段，不做反应避免误操作打断显示
			     if(VshowFSMState!=BattVdis_Waiting)break;
				   //五击按键解除锁定,绿灯闪3次主灯亮0.5秒
				   if(Click==5)
						 {
						 LEDMode=LED_GreenBlinkThird;
						 EnterExitLock();
						 }
			     //N击+长按事件
		       else switch(getSideKeyNClickAndHoldEvent())
							{			
						  case 2: 
								//锁定状态下允许双击+长按查看电压
								TriggerVshowDisplay();
								break; 
							case 1:
								//锁定状态且电池电量充足时单击+长按开启应急低亮
								IsDisplayLocked=1;
							  if(!IsBatteryFault)
									{	
									DisplayLockedTIM=8*EmergencyOFFModeTime;
									break;    
									}
									
							default:
								//开启月光档之后的处理
								if(IsDisplayLocked||DisplayLockedTIM)
									{
									//用户按下按键，或者电池出现问题手动关闭
									if(Click==1||IsBatteryFault)
										{
										DisplayLockedTIM=0;
										break;
										}
									//超时时间到，系统自动关闭
									if(!DisplayLockedTIM)IsDisplayLocked=0;
									}
								//其余任何操作无效，指示手电已被锁定
								if(IsKeyEventOccurred())LEDMode=LED_RedBlinkFifth; 
							  break;
							}				   
				   break;
			//战术模式
			case Operation_TacTurbo:
			case Operation_TacStrobe:
				  //用户四击，退出战术模式
				  if(Click==4)
						 {
						 EnterExitTac();
						 //这里是为了四击退出之后不进入照远光狗模式
						 return Operation_TacTurbo;
						 }
			    //正常战术模式执行
					if(Click==2) //切换模式
						{
						if(SysMode==Operation_TacTurbo)
							{
							SysMode=Operation_TacStrobe;
							LEDMode=LED_GreenBlinkThird; //开启爆闪战术
							}
						else
							{
							SysMode=Operation_TacTurbo;
							LEDMode=LED_RedBlinkThird;  //关闭爆闪战术
							}
						}
					if(getSideKeyHoldEvent())TryEnterTurboStrobeProcess(SysMode==Operation_TacStrobe?3:2); //调用进入函数尝试进极亮
				break;
			}
	//非锁定模式下,或者是电池故障位置起，复位flag
	if(SysMode!=Operation_Locked)IsDisplayLocked=0;
	//所有运算完毕，返回系统状态（直接返回enum就行，因为非0值的话系统就是特殊模式，此时可以让条件成立）
	return SysMode;
	}	
/*********************************  End Of File  ************************************/
