redstoner-35/DFEx-FloodBeaMon3tr/固件/驱动固件源码/include/Logic/Strobe.h

/************************************************************************************/
/** \file Strobe.h
/** \Author redstoner_35
/** \Project Xtern Ripper Hyper Boost HV 4S-GaN Edition
/** \Description 这个头文件为系统顶层逻辑模块的声明文件。该模块声明了实现高频爆闪以及随
机变频混合爆闪的处理模块相关的初始化和逻辑处理函数。

**	History: Initial Release
**	
/************************************************************************************/
#ifndef _Strobe_
#define _Strobe_
/************************************************************************************/
/* Extern Flags and Variable definition */
/************************************************************************************/
extern bit EnableRandomStrobe;

/************************************************************************************/
/* Extern Function definition - Initialization
*************************************************************************************/
void ResetStrobeModule(void);

/************************************************************************************/
/* Extern Function definition - Logic & Strobe Output Handler
*************************************************************************************/
void RandStrobeHandler(void);
bit StrobeOutputHandler(void);

#endif /* _Strobe_ */

/*********************************  End Of File  ************************************/
