redstoner-35/DFEx-FloodBeaMon3tr/固件/驱动固件源码/Logic/SelfTest.c

/****************************************************************************/
/** \file Sleep.c
/** \Author redstoner_35
/** \Project Xtern Ripper Hyper Boost HV 4S-GaN Edition
/** \Description 这个文件为顶层应用层逻辑文件。负责实现系统的运行时自我状态监视
以及错误管理和错误汇报功能，同时该函数实现极亮挡位的自适应MPPT以保护低性能电池。

**	History:
				2026年4月28日 14:40
														 1.针对8串灯珠输出修改系统进行输出异常（如短路，开
															 路和输出过载）的判定条件匹配对应的灯珠
														 3.修改输入MPPT的判定条件针对4串电池做适配
														 
				2025年12月20日 Initial Release
**	
*****************************************************************************/
/****************************************************************************/
/*	include files
*****************************************************************************/
#include "LEDMgmt.h"
#include "delay.h"
#include "ADCCfg.h"
#include "BattDisplay.h"
#include "ModeControl.h"
#include "SelfTest.h"
#include "LowVoltProt.h"
#include "OutputChannel.h"

/****************************************************************************/
/*	Local pre-processor symbols/macros - for Parameter Definition
****************************************************************************/
#define FaultBlankingInterval 3  //每次系统开始运行时，等待系统稳定的错误消隐时间

/****************************************************************************/
/*	Local variable and Flag definitions('static')
****************************************************************************/
static xdata unsigned char ErrDisplayIndex; //错误显示计时
static xdata unsigned char ShortDetectTIM=0; //短路监测计时器
static xdata unsigned char ShortBlankTIM; //短路检测消隐定时器

/****************************************************************************/
/*	Local constant variable definitions('static const 'or 'code')
****************************************************************************/

static code FaultCodeDef NonCriticalFault[]=
	{ 
	//非致命的错误代码
	Fault_DCDCOpen,
  Fault_DCDCShort, //开路和短路可能是误报，允许消除
  Fault_InputOVP
	};
	
/****************************************************************************/
/*	Global variable definitions(declared in header file with 'extern')
****************************************************************************/
bit IsInputLimited;  					//输入限流触发
xdata FaultCodeDef ErrCode; 	//错误代码	
	
/********************************************************************************/
/* Global Function implementation - Error Reporting Logic via LED on Side button
*********************************************************************************/		

//错误ID显示计时函数	
void DisplayErrorTIMHandler(void)	
	{
	//没有错误发生，复位计时器
	if(ErrCode==Fault_None)ErrDisplayIndex=0;
	else //发生错误，开始计时
		{
		ErrDisplayIndex++;
    if(ErrDisplayIndex>=(15+(6*(int)ErrCode)))ErrDisplayIndex=0; //上限到了，开始翻转
		}
	}

//出现错误时显示DCDC的错误ID
void DisplayErrorIDHandler(void)
	{
	int buf;
	//先导提示红黄绿交替闪
  if(ErrDisplayIndex<5)
		{
		if(ErrDisplayIndex<3)LEDMode=(LEDStateDef)(ErrDisplayIndex+1);	
		else LEDMode=LED_OFF;
		}
	//闪烁指定次数显示Err ID
	else if(ErrDisplayIndex<(5+(6*(int)ErrCode)))
		{
		buf=(ErrDisplayIndex-5)/3; 
		if(!(buf%2))LEDMode=LED_Red;
		else LEDMode=LED_OFF;  //按照错误ID闪烁指定次数
		}
  else LEDMode=LED_OFF; //LED熄灭
	}

/********************************************************************************/
/* Global Function implementation - Error Submit/Clear and Query Severe Level
*********************************************************************************/		
	
//查询错误是否致命
bit IsErrorFatal(void)	
	{
	unsigned char i;
	for(i=0;i<sizeof(NonCriticalFault);i++)
		if(NonCriticalFault[i]==ErrCode)return 0;
	//寻找了目前已有的错误码发现是致命问题
	return 1;
	}

//报告错误
void ReportError(FaultCodeDef Code)
	{
	ErrCode=Code;
	if(CurrentMode->ModeIdx==Mode_Fault)return;
	SwitchToGear(Mode_Fault);  //指示故障发生
	}

//消除错误
void ClearError(void)
	{
	ErrCode=Fault_None;
	SwitchToGear(Mode_OFF);
	}

/********************************************************************************/
/* Local Function implementation - Counter for Self Monitoring Logic 
*********************************************************************************/	
static char ErrTIMCounter(char buf,char Count)
	{
	//累加计数器
	return buf<8?buf+Count:8;
	}
	
/********************************************************************************/
/* Global Function implementation - Driver Self Monitoring Logic Handler
*********************************************************************************/
	
//输入MPPT触发限流检测	
void InputLimitedDetect(void)
	{
	//ADC结果已更新，执行一次电流上升
	if(!IsADResultOK)return;
	IsADResultOK=0;
	IsOutputAllowedToRise=1;   //本次AD运算完成，允许执行一次MPPT电流上升

	//输入MPPT限流监测		
	if(Data.RawBattVolt<BeforeRawBattVolt||(Data.FBInjectVolt<0.1&&Data.RawBattVolt<14.2&&Data.OutputVoltage>22))
		{
		//电池总电压低于14.4V，FB注入运放输出拉到负轨且输出大于24V以及压降过大检测触发，说明输入限流触发
	  IsInputLimited=1; 
		}
	//成功置起MPPT标志位且不满足以上条件，输入限流解除
	else if(IsCurrentRampUp)IsInputLimited=0;
	}	
	
//输出故障检测
void OutputFaultDetect(void)
	{
	char buf,OErrID;
	//输出故障监测
	if(!GetIfOutputEnabled())ShortBlankTIM=0; //DCDC关闭
	else if(ShortBlankTIM<FaultBlankingInterval)ShortBlankTIM++; //时间未到不允许监测
	else  //开始检测
		{		
		buf=ShortDetectTIM&0x0F; //取出定时器值					
		//输入过压保护
		if(Data.BatteryVoltage>4.4)ReportError(Fault_InputOVP); 
		//短路检测	
		if(Data.OutputVoltage<19&&Data.FBInjectVolt>4.8) //输出短路
			{
			buf=ErrTIMCounter(buf,2); //计时器累计
			OErrID=0;
			}
		//输出开路检测
		else if(Data.FBInjectVolt<0.5&&Data.OutputVoltage>32.8) 
			{
			buf=ErrTIMCounter(buf,1); //计时器累计
			OErrID=1;
			}
		else buf=buf>0?buf-1:0; //没有发生错误，清除计数器
		//进行定时器数值的回写
		ShortDetectTIM=buf|(OErrID<<4);
		//状态检测
		if(buf<8)return; //没有故障,跳过执行
		switch((ShortDetectTIM>>4)&0x0F)	
			{
			case 1:ReportError(Fault_DCDCOpen);break;
			default:ReportError(Fault_DCDCShort);
			}
		}
	}
/*********************************  End Of File  ************************************/
